Mikster4/thesis/Code/data/combined_rotation.png

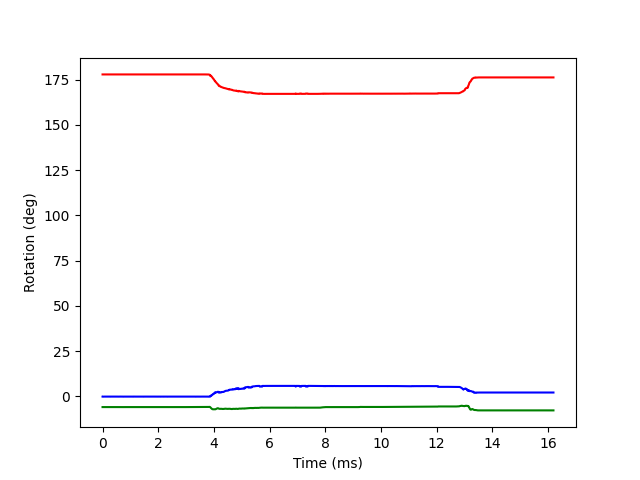
Code/data/combined_rotation.png
