Mikster4/thesis/Code/data/combined_rotation_relative.png

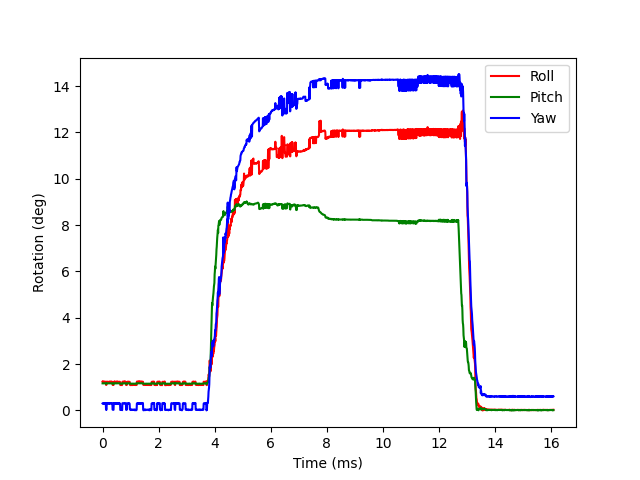
Code/data/combined_rotation_relative.png
