Mikster4/thesis/Code/data/Location_0_XY.PNG

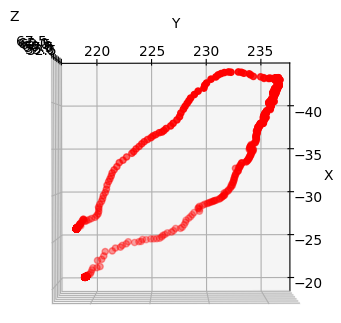
Code/data/Location_0_XY.PNG
