Mikster4/thesis/Code/data/Location_0_XZ.PNG

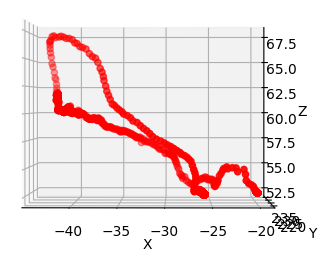
Code/data/Location_0_XZ.PNG
