Mikster4/thesis/Code/data/Location_0_YZ.PNG

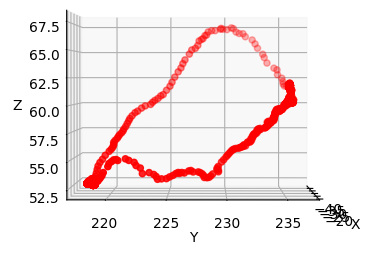
Code/data/Location_0_YZ.PNG
