Mikster4/thesis/Code/data/Max_Roll_Rotation_Norm.png

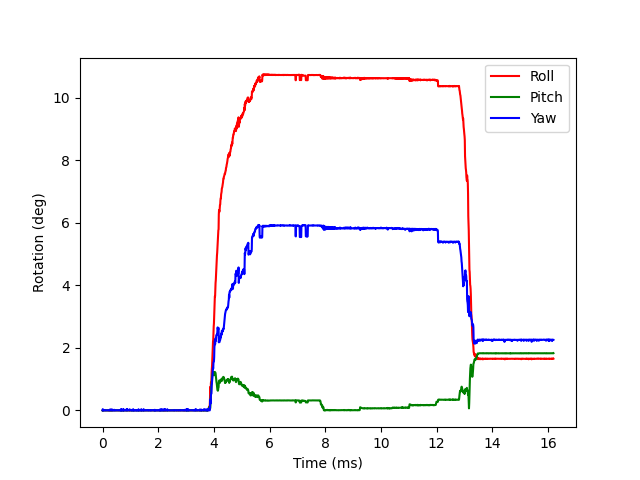
Code/data/Max_Roll_Rotation_Norm.png
