Mikster4/thesis/Code/data/Max_Yaw_Rotation_Raw.png

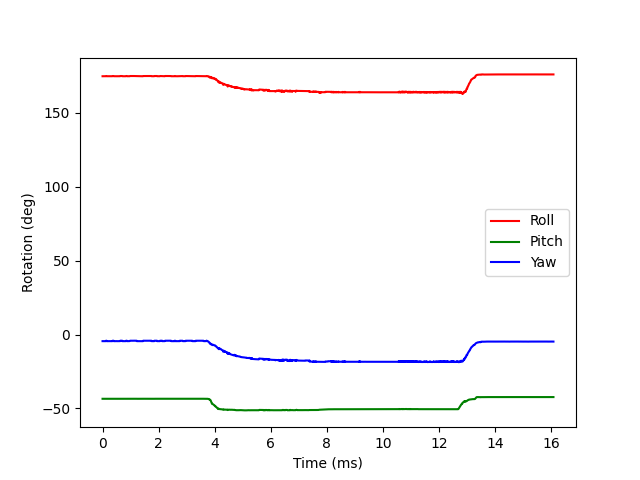
Code/data/Max_Yaw_Rotation_Raw.png
