Mikster4/thesis/CODE/data/pitch.png

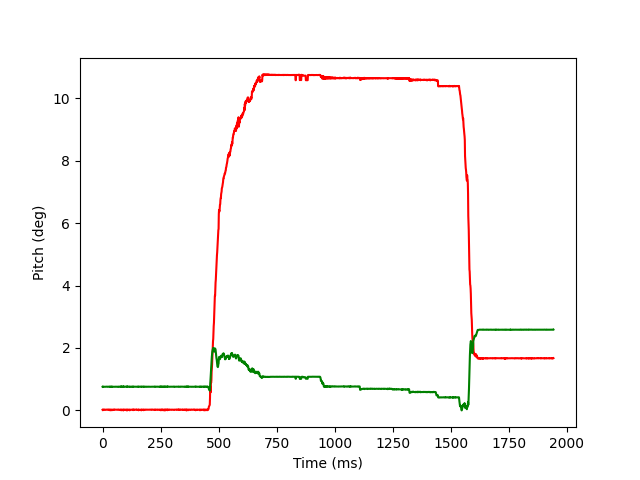
CODE/data/pitch.png
