Mikster4/thesis/Code/data/Platform_Linear.png

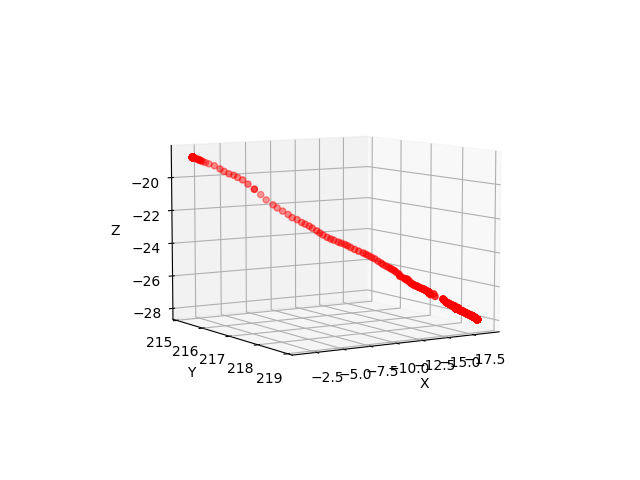
Code/data/Platform_Linear.png
