Mikster4/thesis/Code/data/platform_shape.PNG

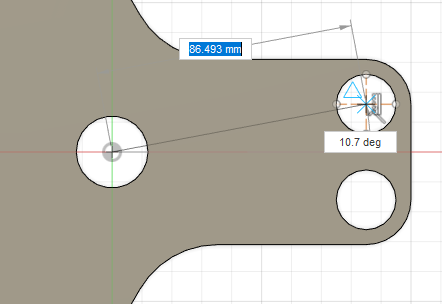
Code/data/platform_shape.PNG
