Mikster4/thesis/CODE/data/yaw.png

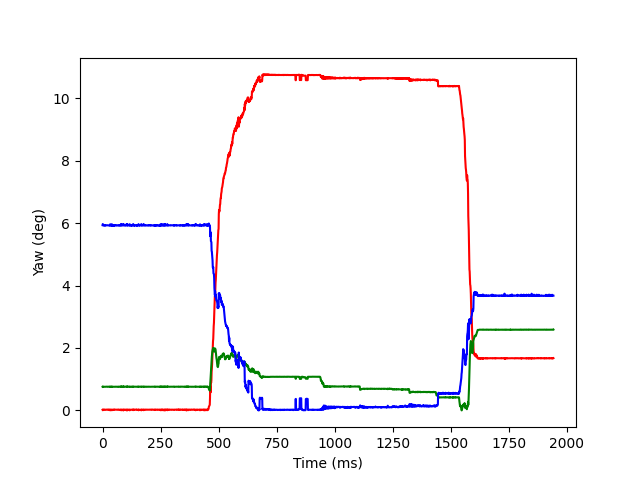
CODE/data/yaw.png
