Mikster4/thesis/IMG/coord.png

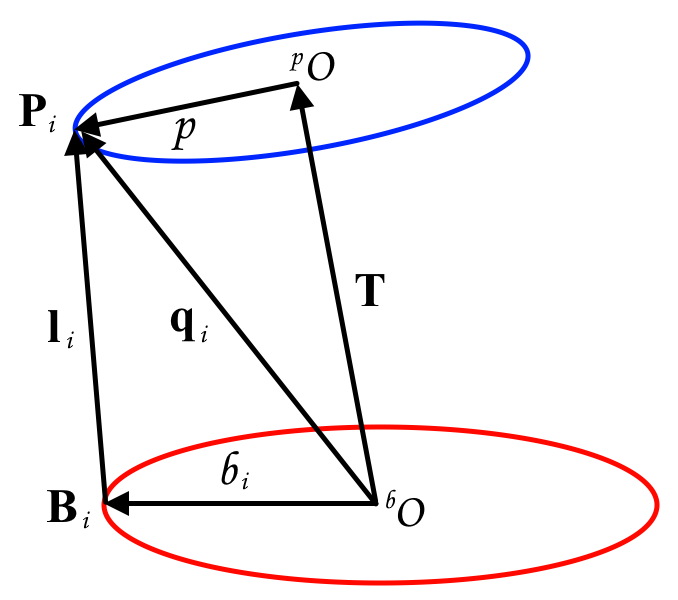
IMG/coord.png
