Mikster4/thesis/IMG/Photos/Cores/final_core_nozzle.jpg

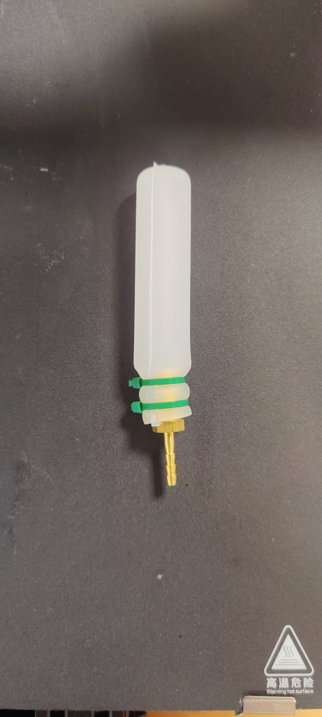
IMG/Photos/Cores/final_core_nozzle.jpg
