Mikster4/thesis/IMG/Photos/Cores/final_mold_cast.jpg

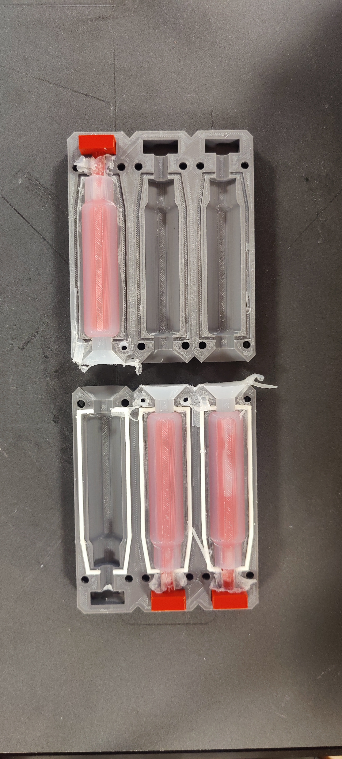
IMG/Photos/Cores/final_mold_cast.jpg
