Mikster4/thesis/IMG/Photos/Cores/IMG_20221129_133544.jpg

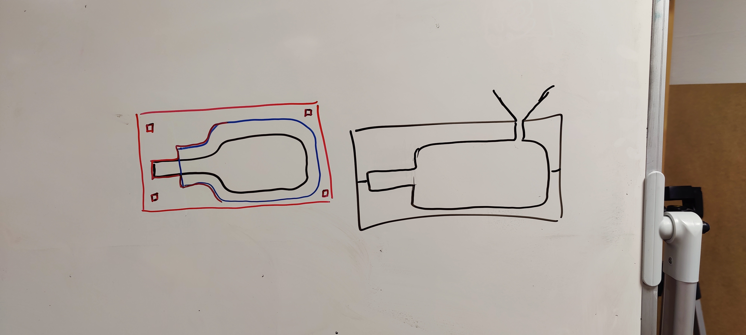
IMG/Photos/Cores/IMG_20221129_133544.jpg
