Mikster4/thesis/IMG/Photos/Cores/IMG_20221201_124950.jpg

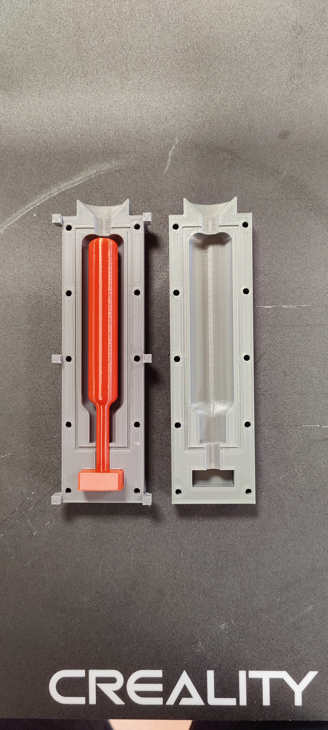
IMG/Photos/Cores/IMG_20221201_124950.jpg
