Mikster4/thesis/IMG/Photos/Cores/IMG_20221201_132122.jpg

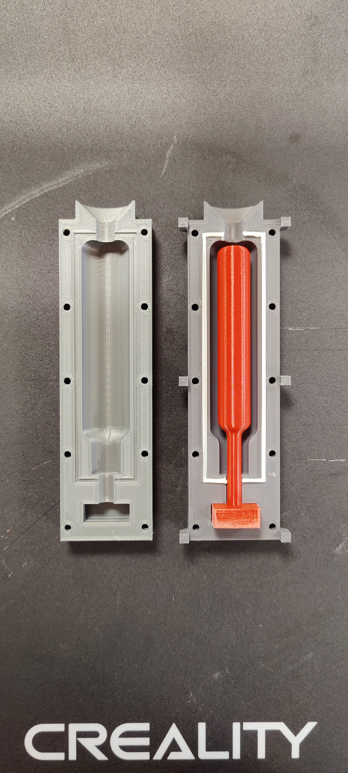
IMG/Photos/Cores/IMG_20221201_132122.jpg
