Mikster4/thesis/IMG/Photos/Cores/IMG_20221201_132601.jpg

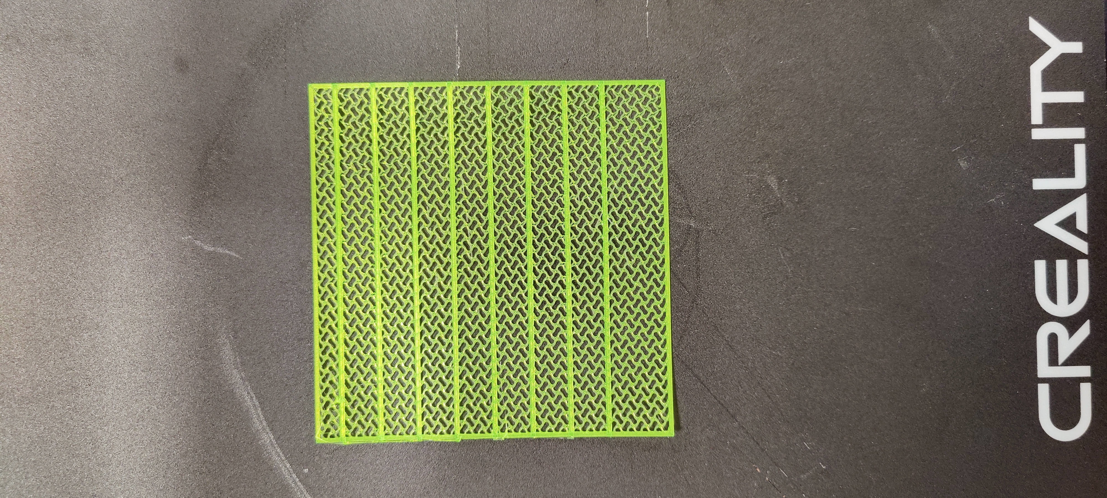
IMG/Photos/Cores/IMG_20221201_132601.jpg
