Mikster4/thesis/IMG/Photos/Cores/IMG_20221201_133057.jpg

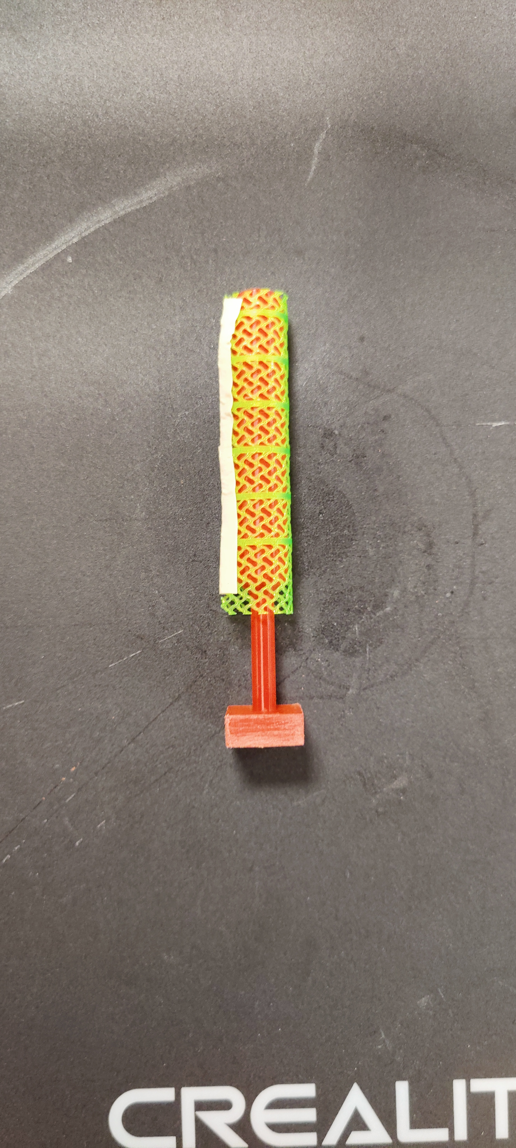
IMG/Photos/Cores/IMG_20221201_133057.jpg
