Mikster4/thesis/IMG/Photos/Cores/IMG_20221201_133152.jpg

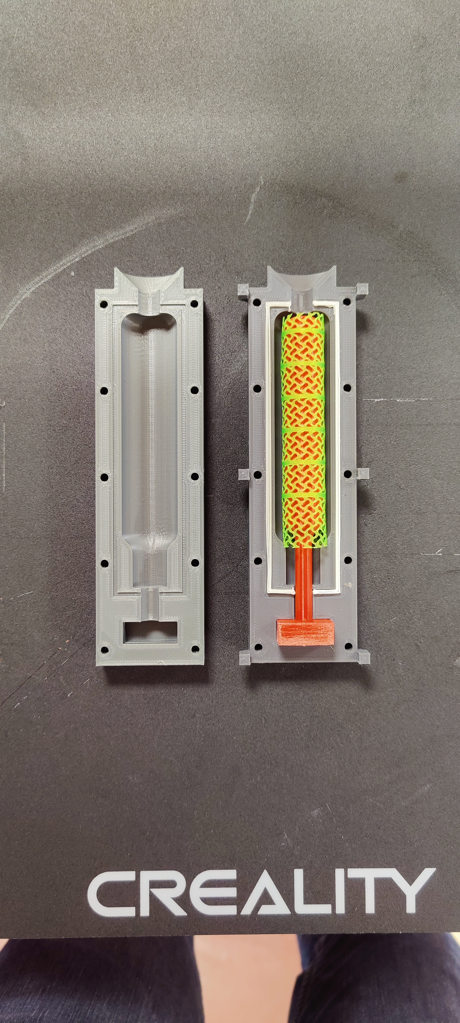
IMG/Photos/Cores/IMG_20221201_133152.jpg
