Mikster4/thesis/IMG/Photos/Cores/IMG_20230104_114442.jpg

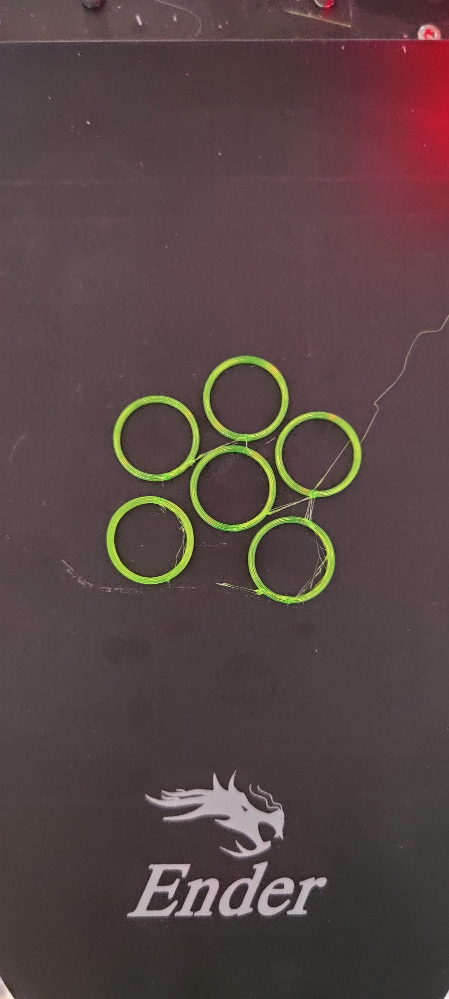
IMG/Photos/Cores/IMG_20230104_114442.jpg
