Mikster4/thesis/IMG/Photos/Cores/IMG_20230104_140045.jpg

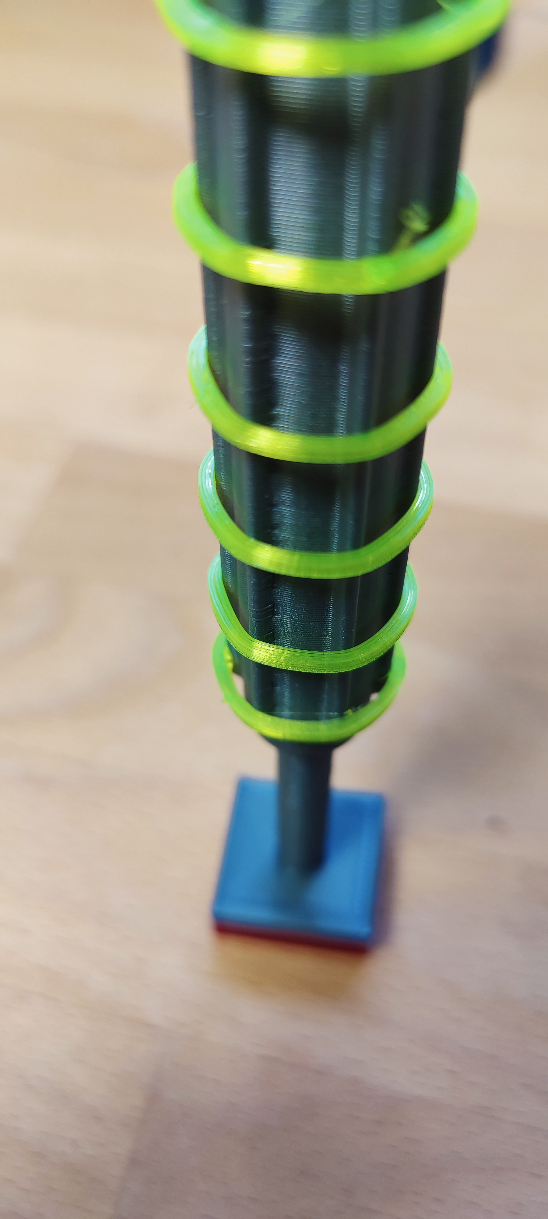
IMG/Photos/Cores/IMG_20230104_140045.jpg
