Mikster4/thesis/IMG/Photos/Cores/IMG_20230104_140136.jpg

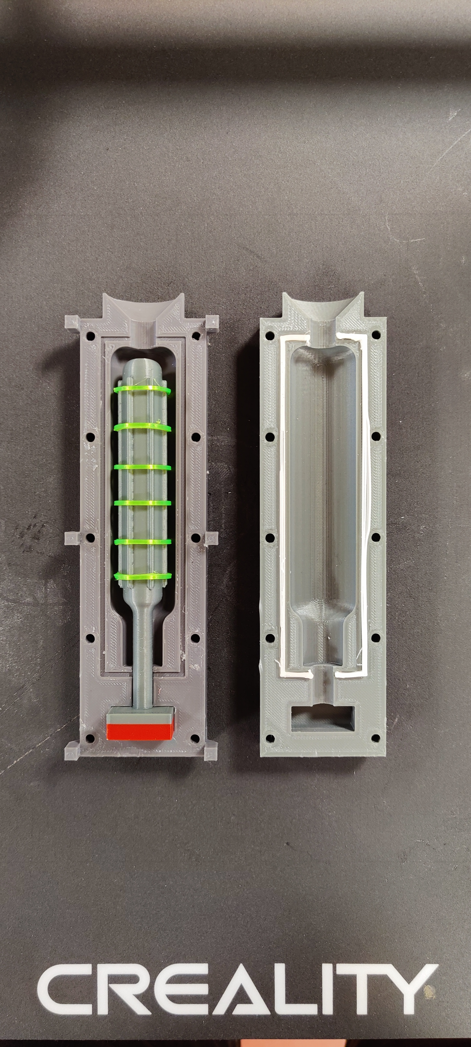
IMG/Photos/Cores/IMG_20230104_140136.jpg
