Mikster4/thesis/IMG/Photos/Cores/IMG_20230105_142405.jpg

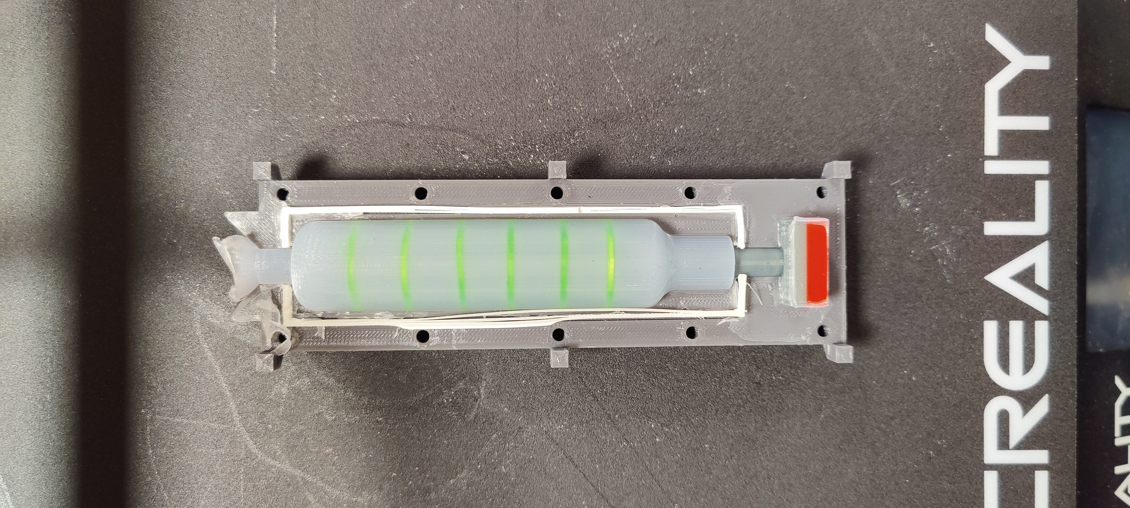
IMG/Photos/Cores/IMG_20230105_142405.jpg
