Mikster4/thesis/IMG/Photos/Cores/IMG_20230105_143052.jpg

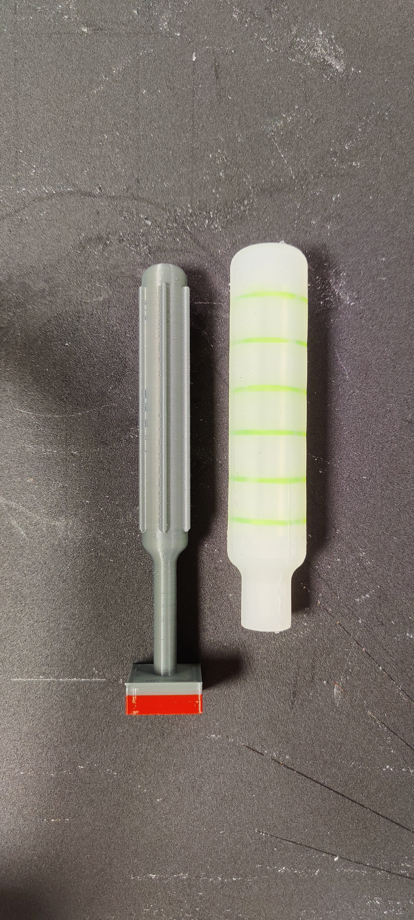
IMG/Photos/Cores/IMG_20230105_143052.jpg
