Mikster4/thesis/IMG/Photos/Cores/IMG_20230105_143107.jpg

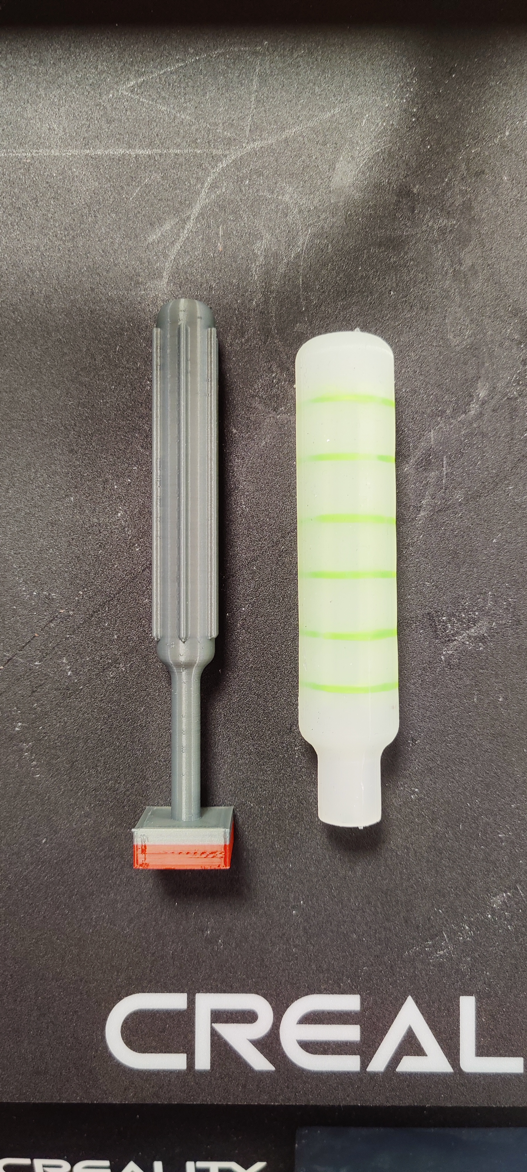
IMG/Photos/Cores/IMG_20230105_143107.jpg
