Mikster4/thesis/IMG/Photos/Cores/IMG_20230112_104922.jpg

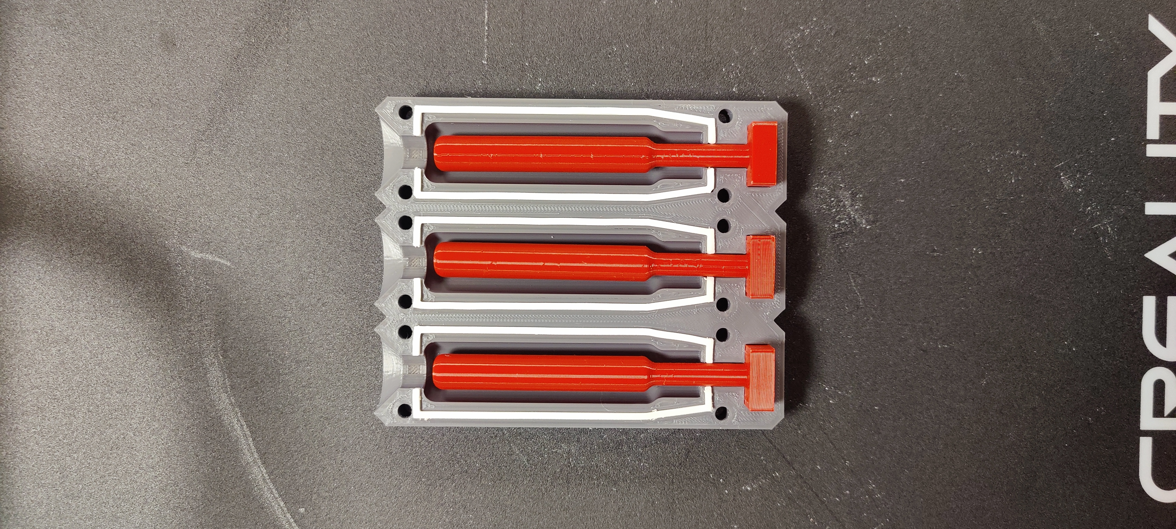
IMG/Photos/Cores/IMG_20230112_104922.jpg
