Mikster4/thesis/IMG/Photos/Cores/IMG_20230112_104932.jpg

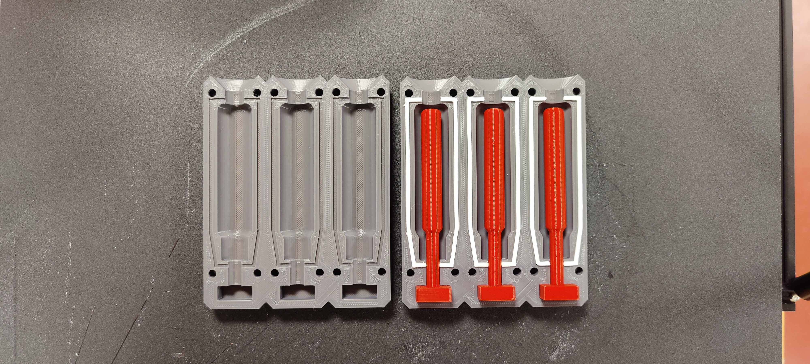
IMG/Photos/Cores/IMG_20230112_104932.jpg
