Mikster4/thesis/IMG/Photos/Cores/IMG_20230119_000719.jpg

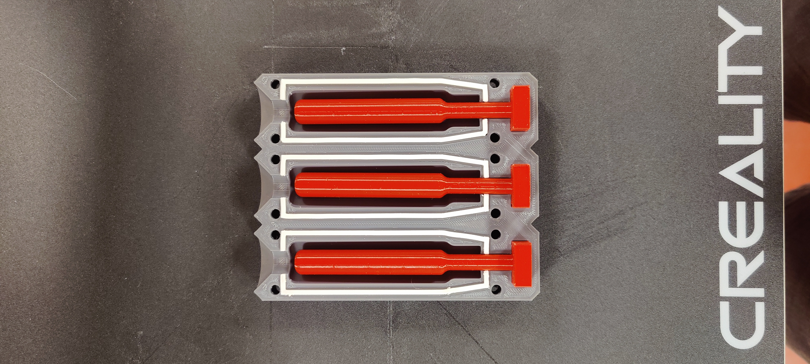
IMG/Photos/Cores/IMG_20230119_000719.jpg
