Mikster4/thesis/IMG/Photos/Cores/IMG_20230119_070848.jpg

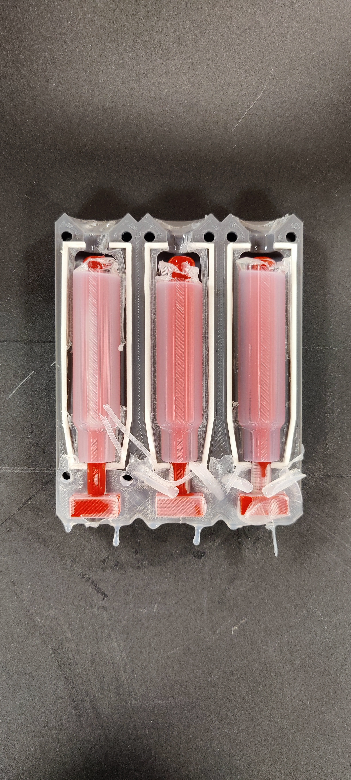
IMG/Photos/Cores/IMG_20230119_070848.jpg
