Mikster4/thesis/IMG/Photos/Cores/IMG_20230119_092744.jpg

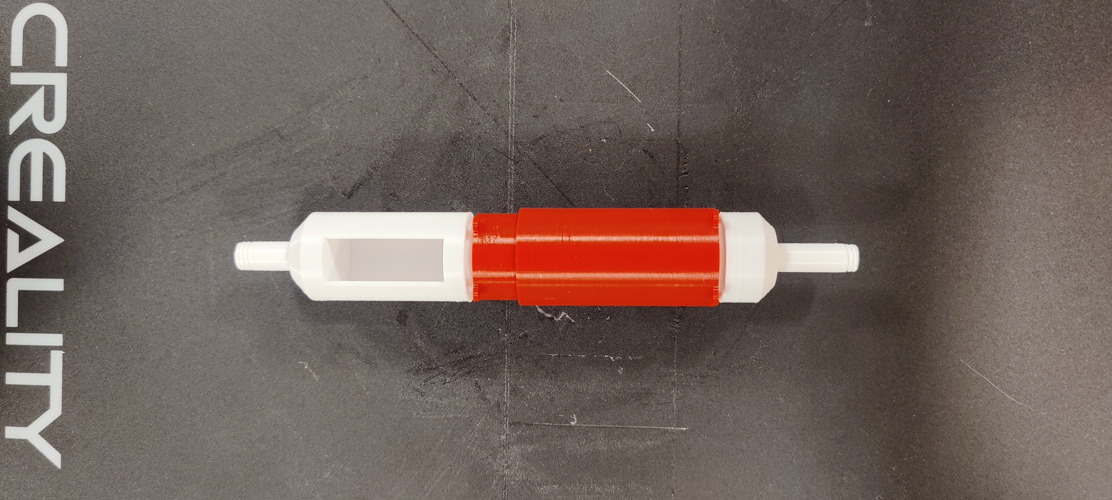
IMG/Photos/Cores/IMG_20230119_092744.jpg
