Mikster4/thesis/IMG/Photos/Cores/IMG_20230119_103604.jpg

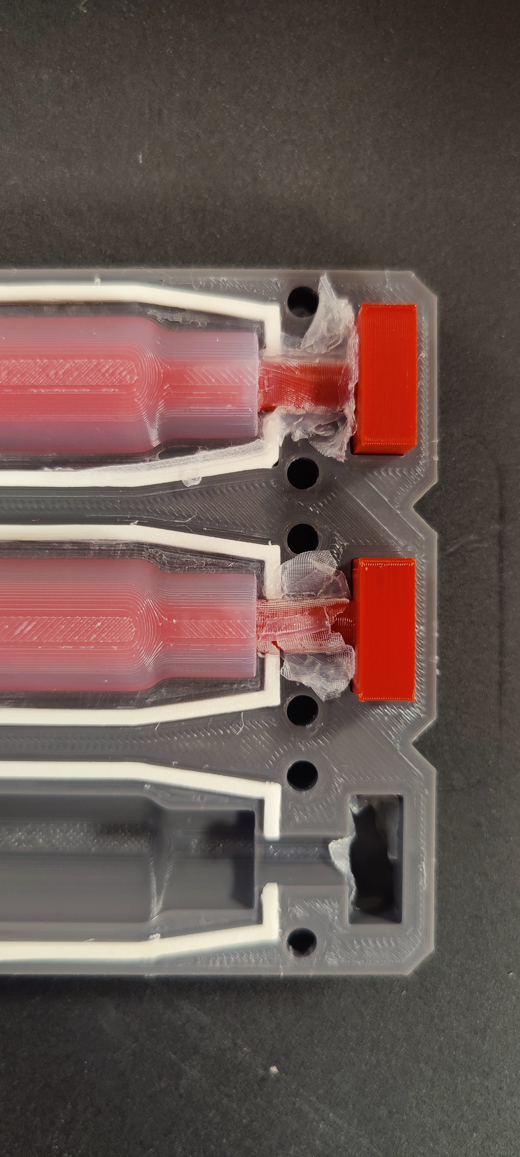
IMG/Photos/Cores/IMG_20230119_103604.jpg
