Mikster4/thesis/IMG/Photos/Cores/IMG_20230119_103908.jpg

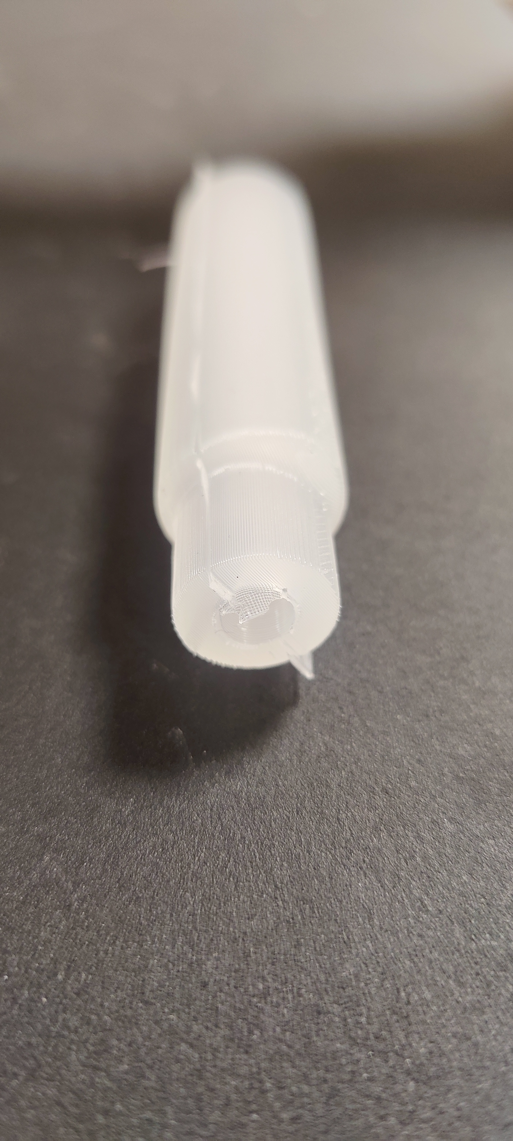
IMG/Photos/Cores/IMG_20230119_103908.jpg
