Mikster4/thesis/IMG/Photos/Cores/IMG_20230221_175424.jpg

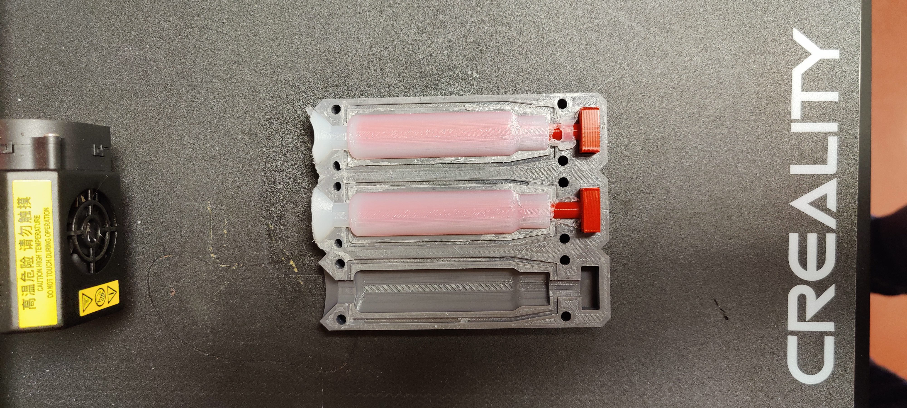
IMG/Photos/Cores/IMG_20230221_175424.jpg
