Mikster4/thesis/IMG/Photos/Cores/IMG_20230221_175434.jpg

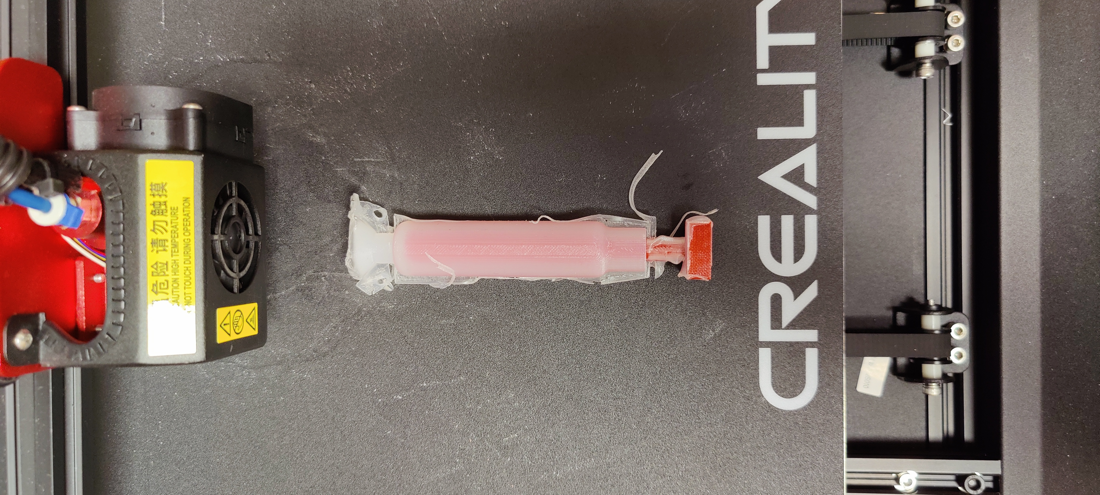
IMG/Photos/Cores/IMG_20230221_175434.jpg
