Mikster4/thesis/IMG/Photos/Cores/mesh_airtight.jpg

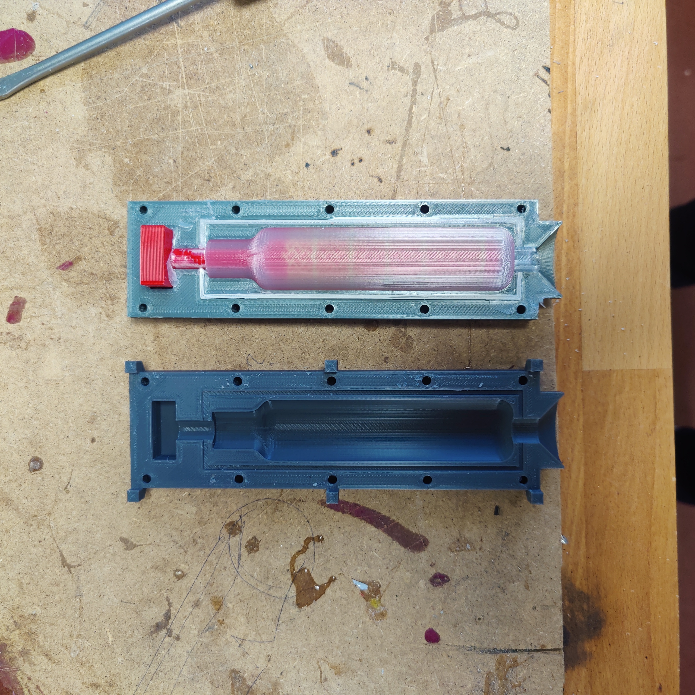
IMG/Photos/Cores/mesh_airtight.jpg
