Mikster4/thesis/IMG/Photos/Cores/mesh_fail_1.jpg

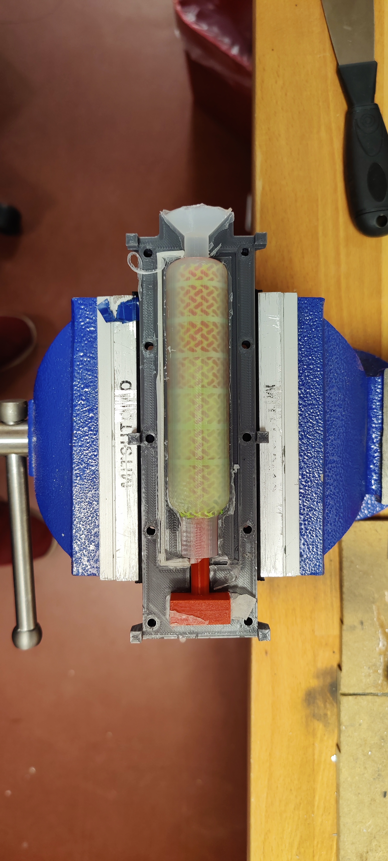
IMG/Photos/Cores/mesh_fail_1.jpg
