Mikster4/thesis/IMG/Photos/Cores/tpu_rings_fail.jpg

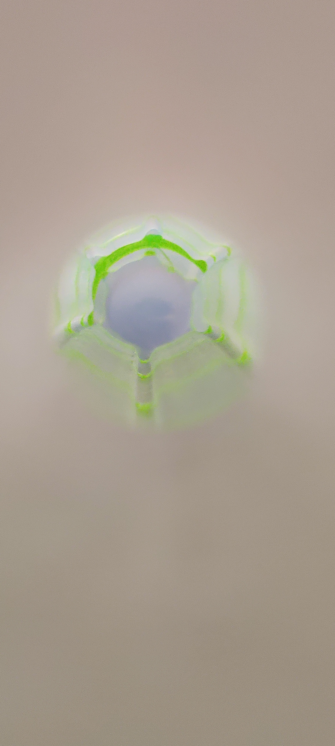
IMG/Photos/Cores/tpu_rings_fail.jpg
