Mikster4/thesis/IMG/Photos/Cores/tpu_rings_finish.jpg

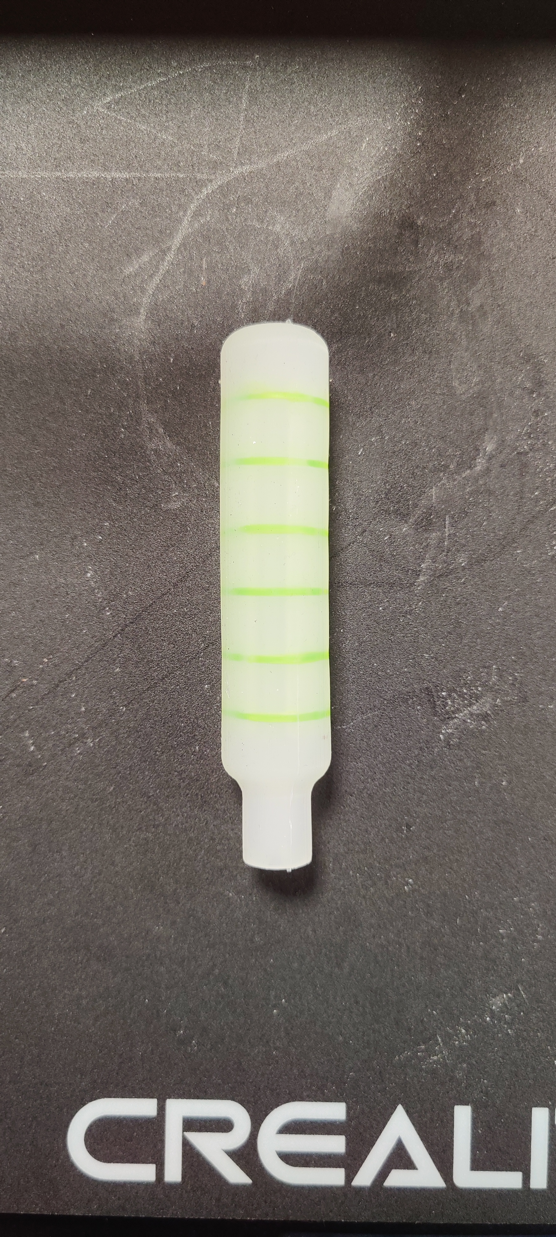
IMG/Photos/Cores/tpu_rings_finish.jpg
