Mikster4/thesis/IMG/Photos/Cores/tpu_rings_insert.jpg

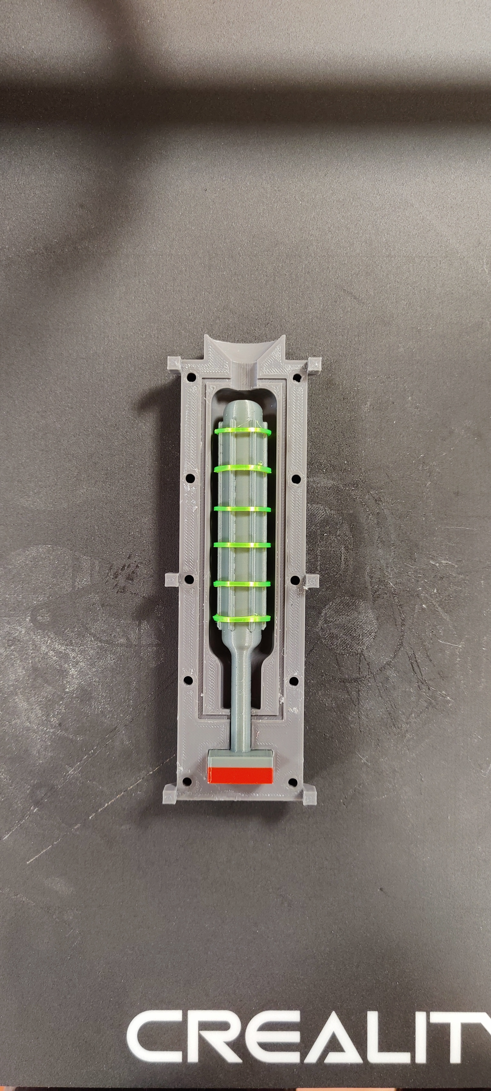
IMG/Photos/Cores/tpu_rings_insert.jpg
