Mikster4/thesis/IMG/Photos/Electrical/IMG_20230119_111654.jpg

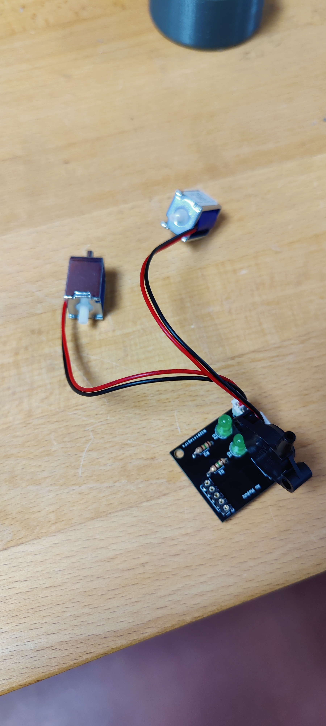
IMG/Photos/Electrical/IMG_20230119_111654.jpg
