Mikster4/thesis/IMG/Photos/Electrical/IMG_20230119_111658.jpg

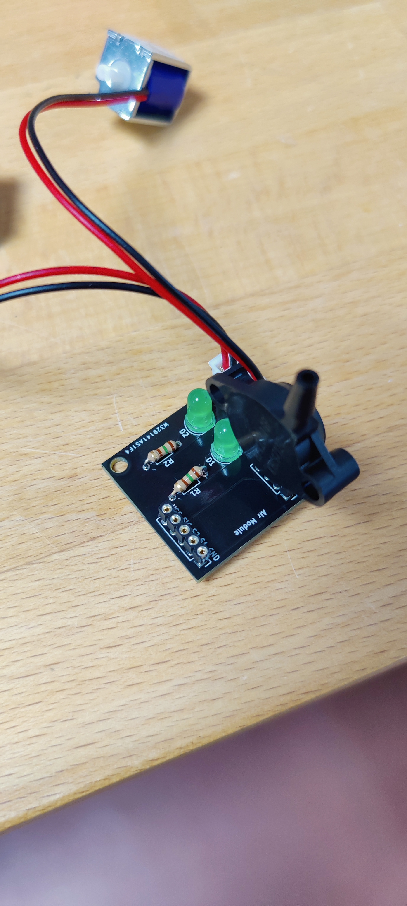
IMG/Photos/Electrical/IMG_20230119_111658.jpg
