Mikster4/thesis/IMG/Photos/Electrical/IMG_20230218_131912.jpg

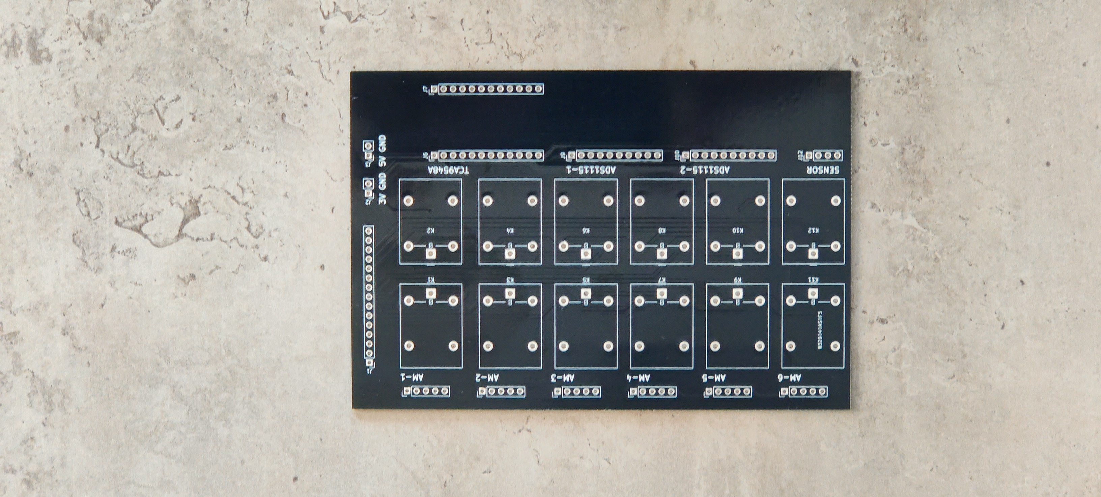
IMG/Photos/Electrical/IMG_20230218_131912.jpg
