Mikster4/thesis/IMG/Photos/Electrical/IMG_20230222_151632.jpg

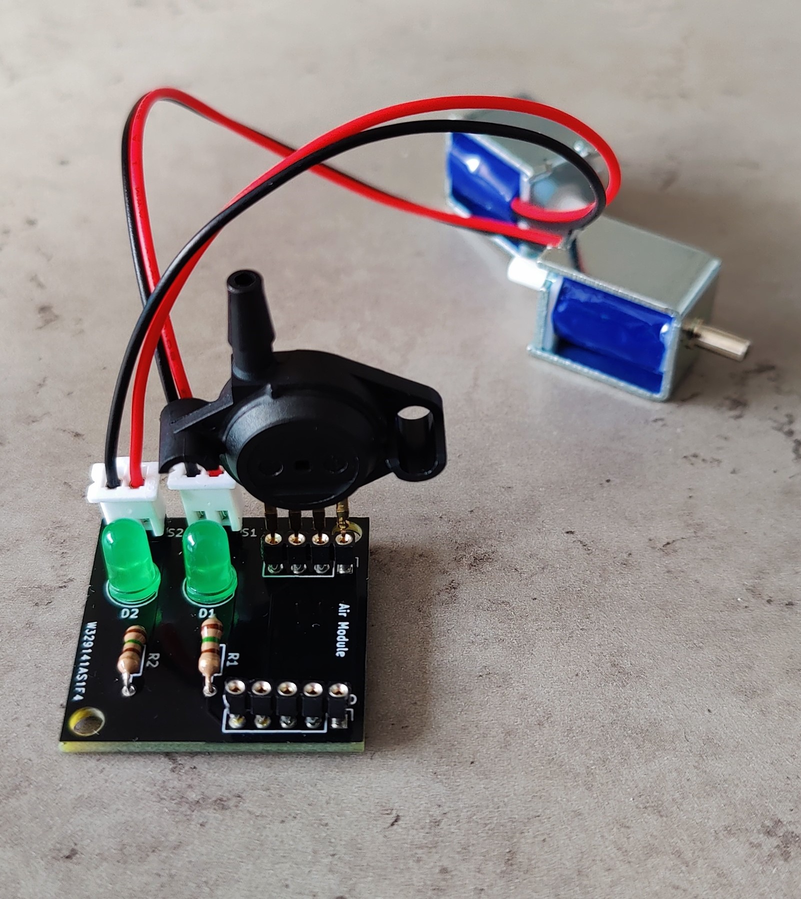
IMG/Photos/Electrical/IMG_20230222_151632.jpg
