Mikster4/thesis/IMG/Photos/Electrical/IMG_20230222_151733.jpg

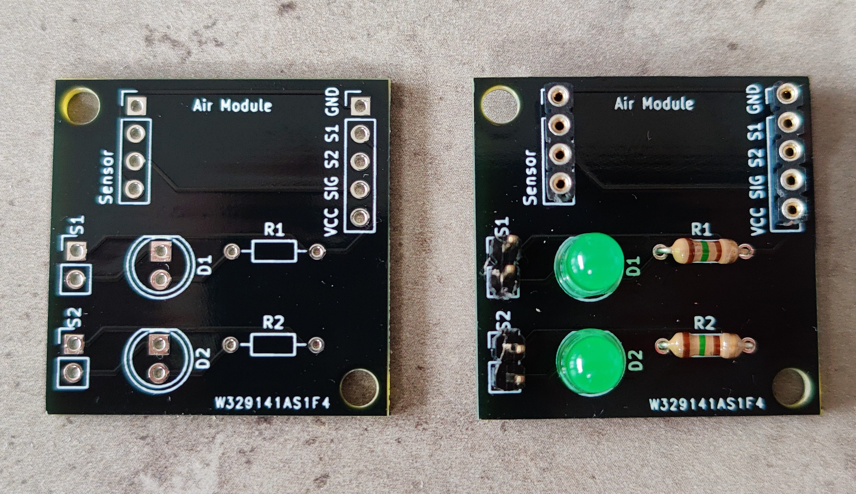
IMG/Photos/Electrical/IMG_20230222_151733.jpg
