Mikster4/thesis/IMG/Photos/OptiTrack/roll_max.png

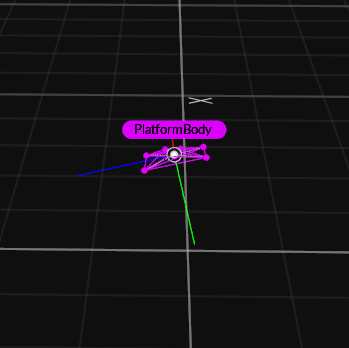
IMG/Photos/OptiTrack/roll_max.png
