Mikster4/thesis/IMG/Photos/OptiTrack/roll_min.png

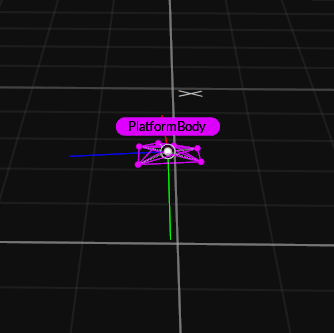
IMG/Photos/OptiTrack/roll_min.png
