Mikster4/thesis/IMG/Photos/OptiTrack/Screenshot 2023-03-09 115746.png

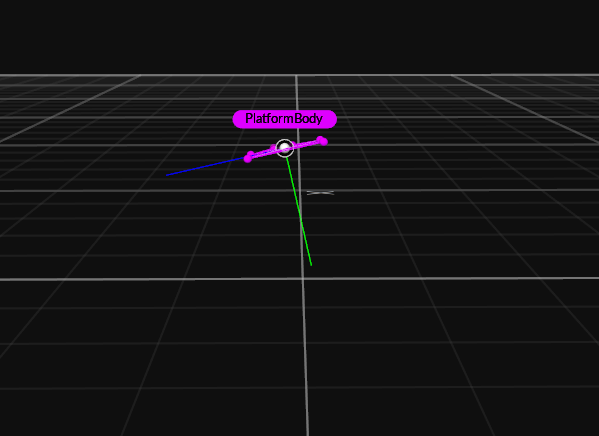
IMG/Photos/OptiTrack/Screenshot 2023-03-09 115746.png
