Mikster4/thesis/IMG/Photos/OptiTrack/yaw_max.png

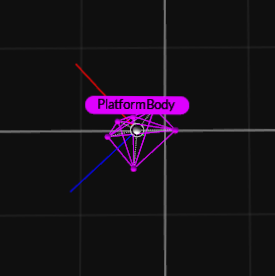
IMG/Photos/OptiTrack/yaw_max.png
