Mikster4/thesis/IMG/Photos/Platform/IMG_20230112_014713.jpg

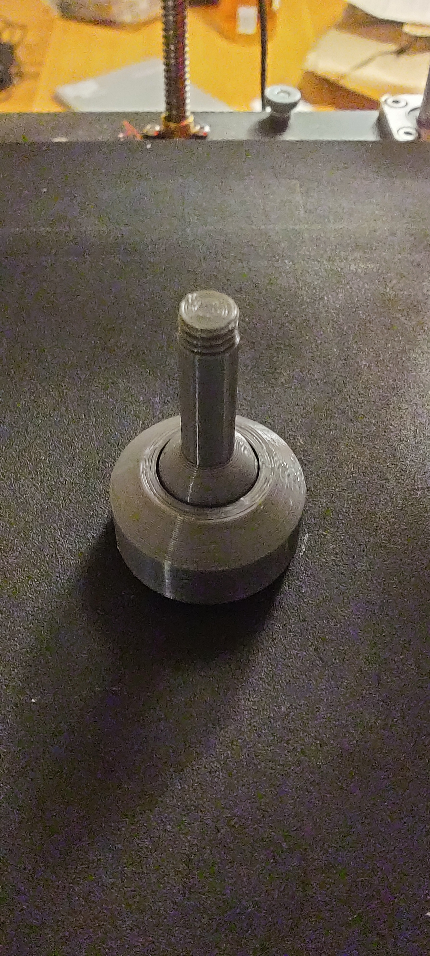
IMG/Photos/Platform/IMG_20230112_014713.jpg
