Mikster4/thesis/IMG/Photos/Platform/IMG_20230112_025201.jpg

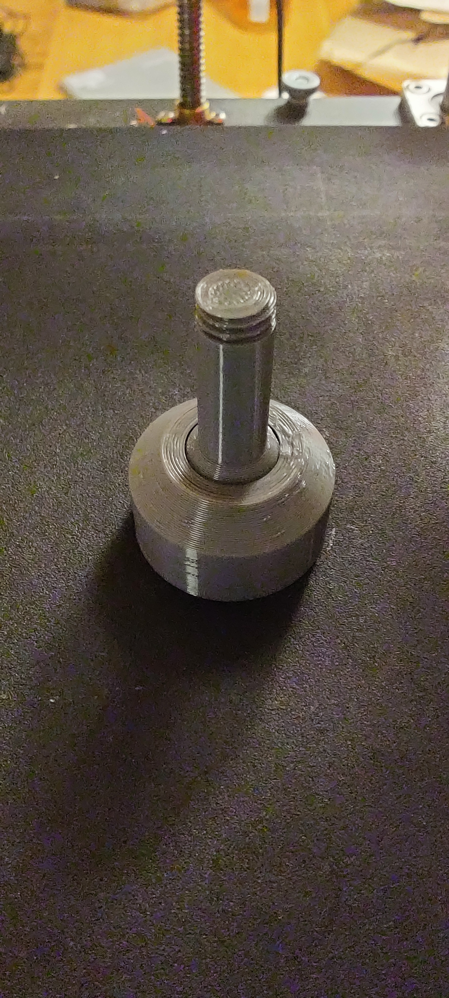
IMG/Photos/Platform/IMG_20230112_025201.jpg
