Mikster4/thesis/IMG/Photos/Platform/IMG_20230119_092630.jpg

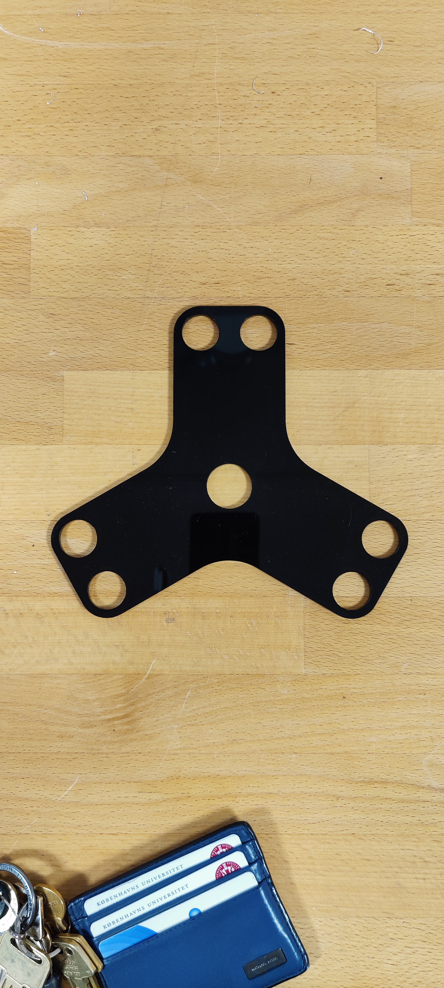
IMG/Photos/Platform/IMG_20230119_092630.jpg
