Mikster4/thesis/IMG/Photos/Platform/IMG_20230119_111612.jpg

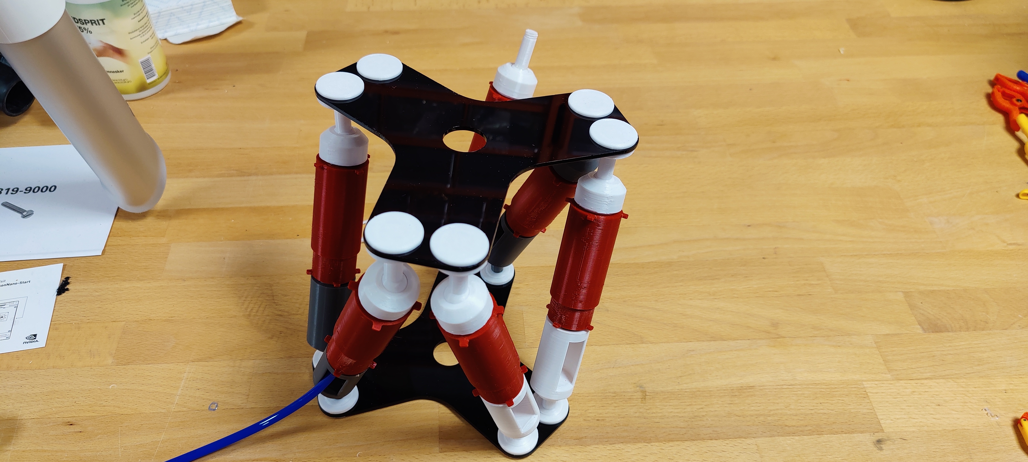
IMG/Photos/Platform/IMG_20230119_111612.jpg
