Mikster4/thesis/IMG/Photos/Platform/IMG_20230119_111621.jpg

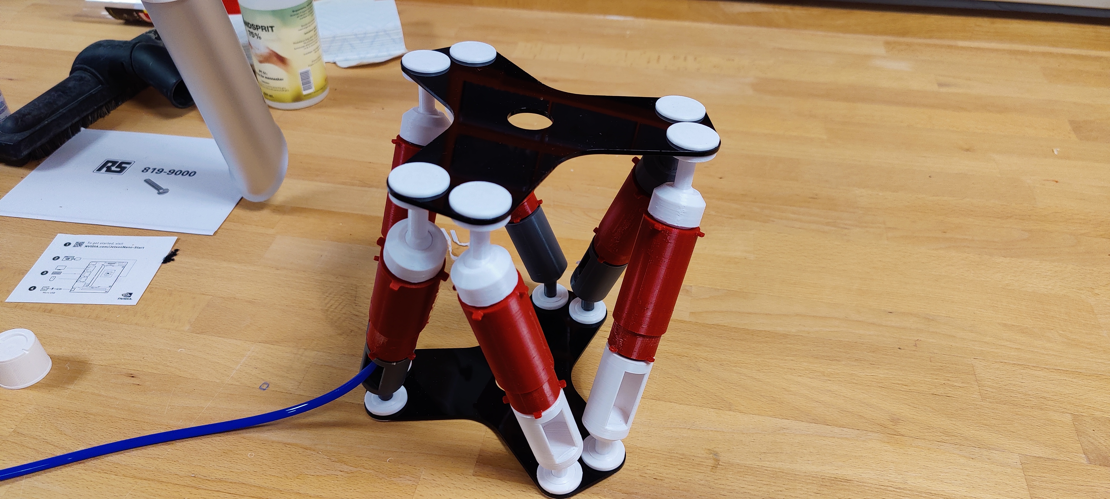
IMG/Photos/Platform/IMG_20230119_111621.jpg
