Mikster4/thesis/IMG/Photos/Platform/IMG_20230222_152040.jpg

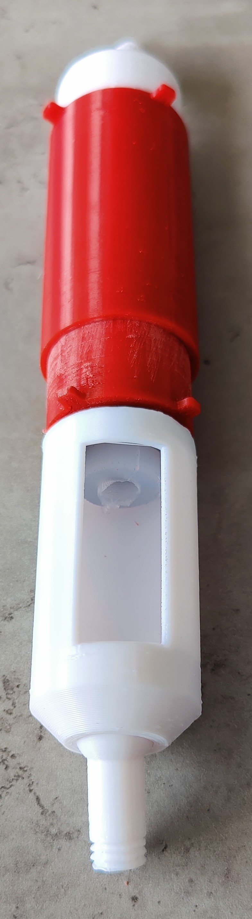
IMG/Photos/Platform/IMG_20230222_152040.jpg
