Mikster4/thesis/IMG/Photos/Platform/IMG_20230222_152114.jpg

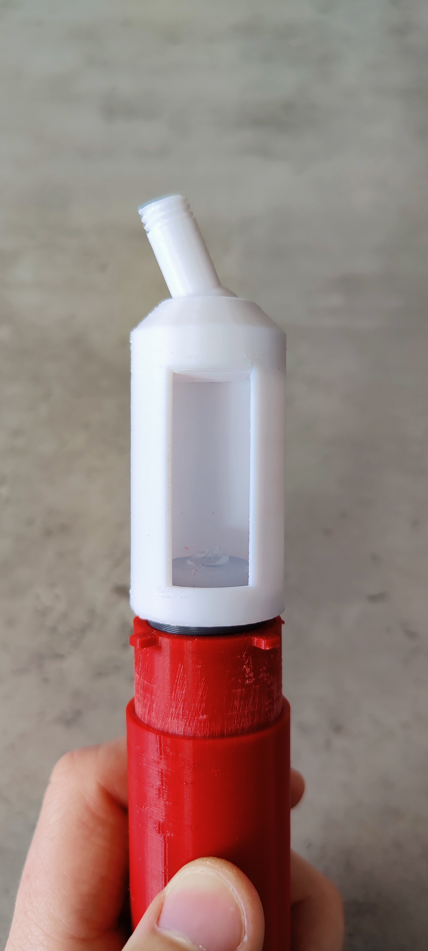
IMG/Photos/Platform/IMG_20230222_152114.jpg
