Mikster4/thesis/IMG/Photos/Platform/IMG_20230222_152124.jpg

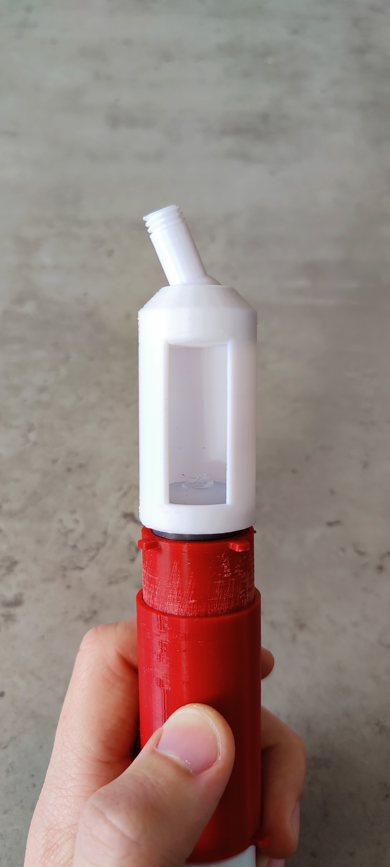
IMG/Photos/Platform/IMG_20230222_152124.jpg
