Mikster4/thesis/IMG/Photos/Platform/IMG_20230222_152329.jpg

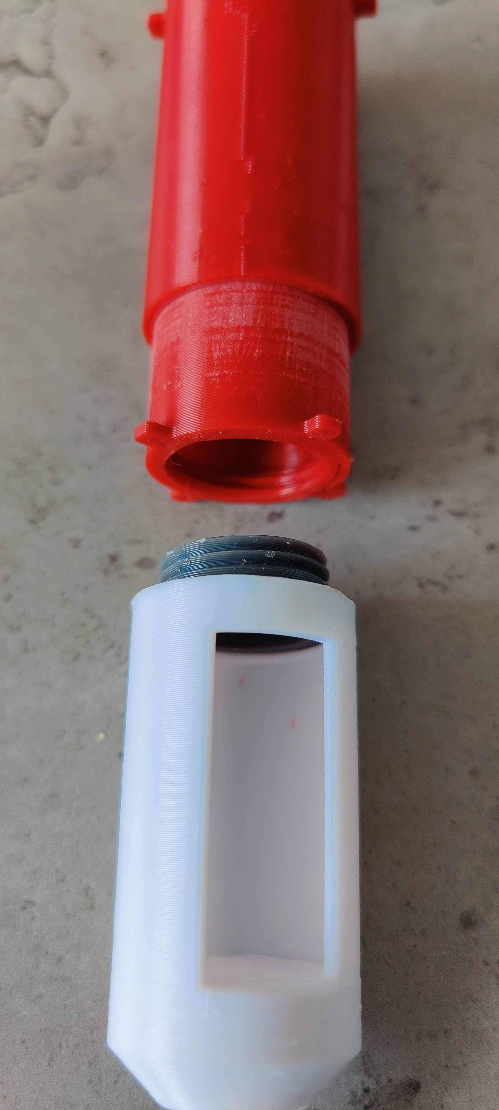
IMG/Photos/Platform/IMG_20230222_152329.jpg
