Mikster4/thesis/IMG/Renders/poc_0.png

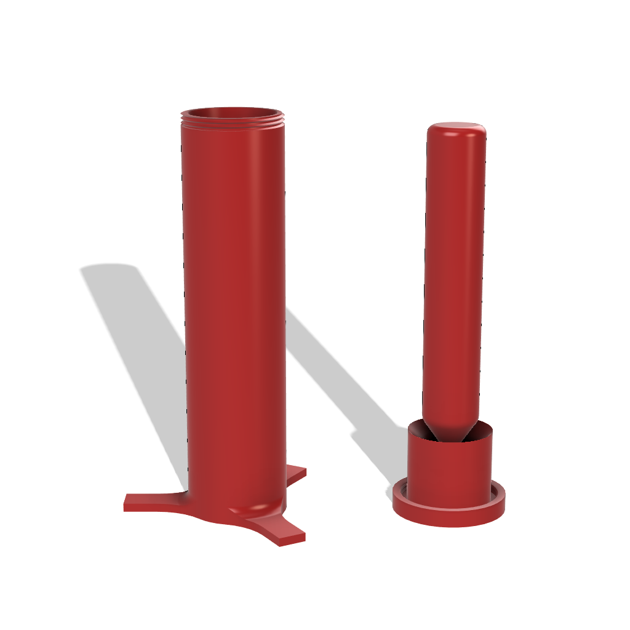
IMG/Renders/poc_0.png
