Mikster4/thesis/IMG/Renders/POC_0_insert.PNG

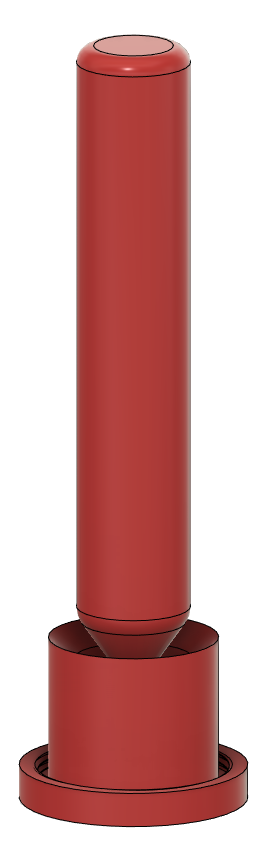
IMG/Renders/POC_0_insert.PNG
