Mikster4/thesis/IMG/Renders/POC_0_insert_cut.PNG

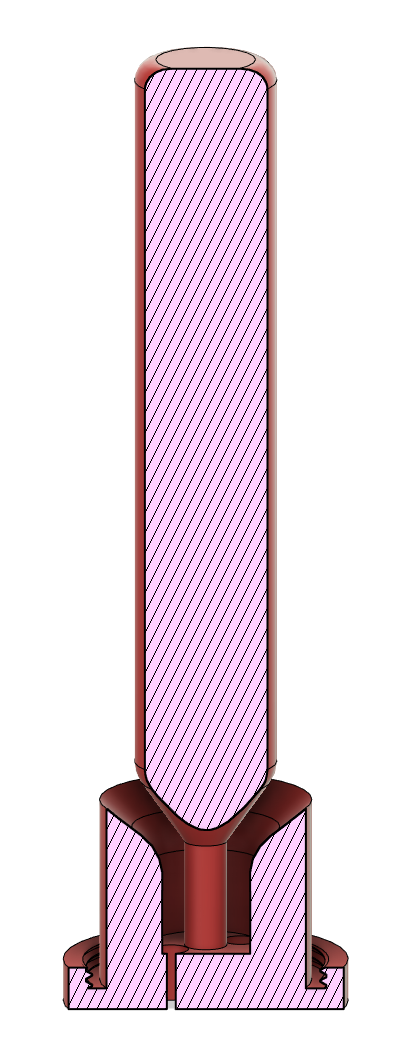
IMG/Renders/POC_0_insert_cut.PNG
