Mikster4/thesis/IMG/Renders/POC_0_shell.PNG

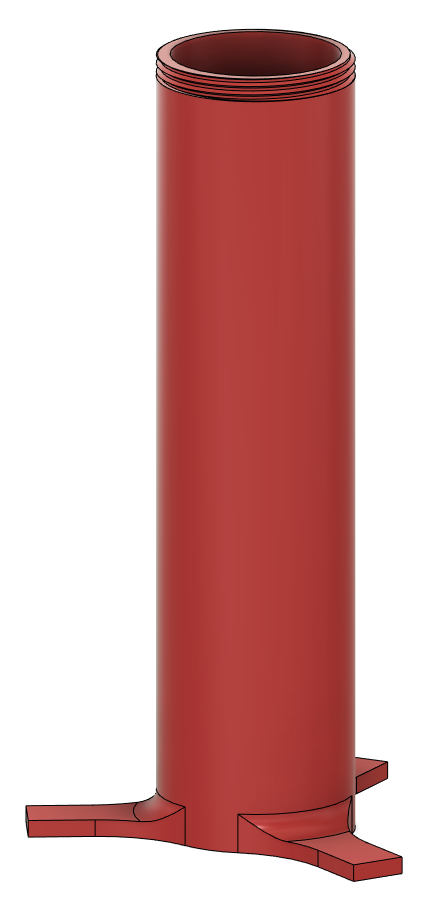
IMG/Renders/POC_0_shell.PNG
