Mikster4/thesis/IMG/Renders/POC_0_shell_cut.PNG

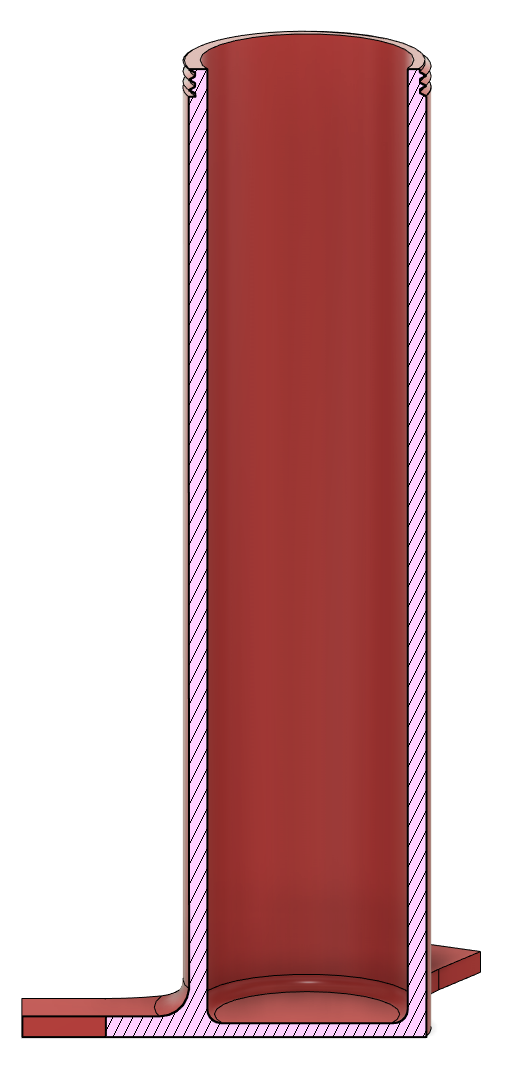
IMG/Renders/POC_0_shell_cut.PNG
