Mikster4/thesis/IMG/Renders/POC_1_Base.PNG

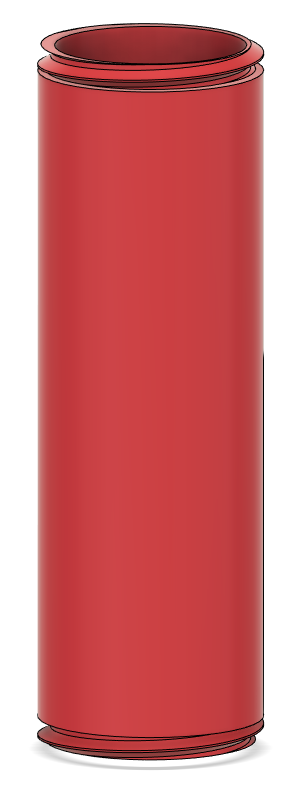
IMG/Renders/POC_1_Base.PNG
