Mikster4/thesis/IMG/Renders/POC_1_Cap.PNG

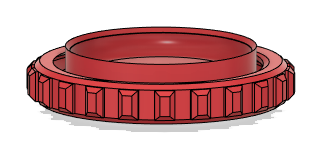
IMG/Renders/POC_1_Cap.PNG
