Mikster4/thesis/IMG/Renders/POC_1_Insert.PNG

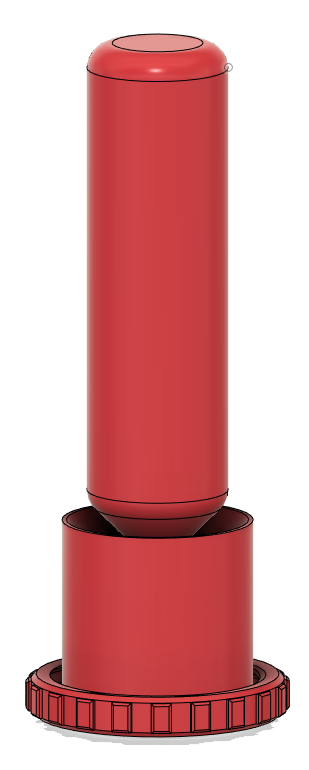
IMG/Renders/POC_1_Insert.PNG
