Mikster4/thesis/IMG/Renders/POC_1_open_top.PNG

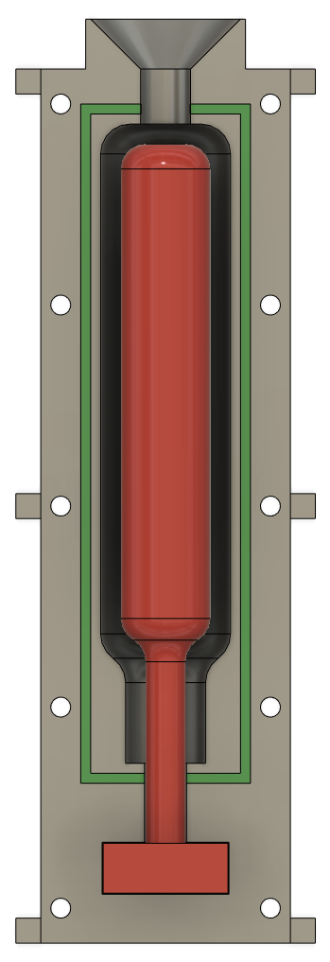
IMG/Renders/POC_1_open_top.PNG
