Mikster4/thesis/IMG/Renders/POC_2_Closed.PNG

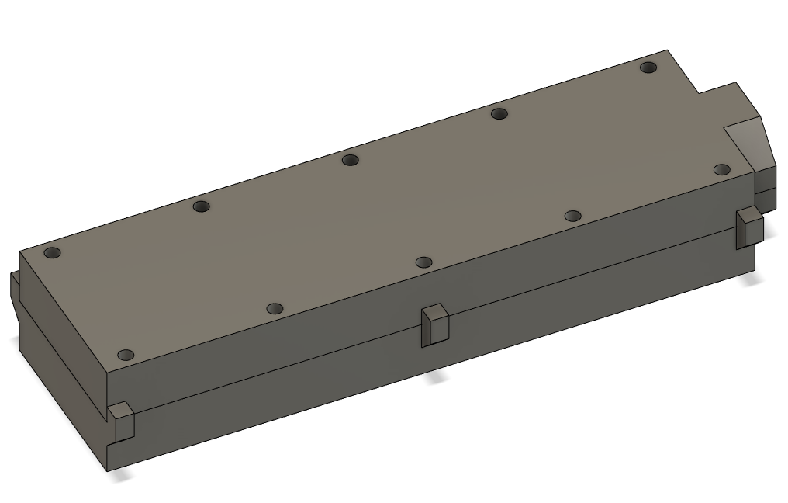
IMG/Renders/POC_2_Closed.PNG
