Mikster4/thesis/IMG/Renders/POC_2_Exploded.PNG

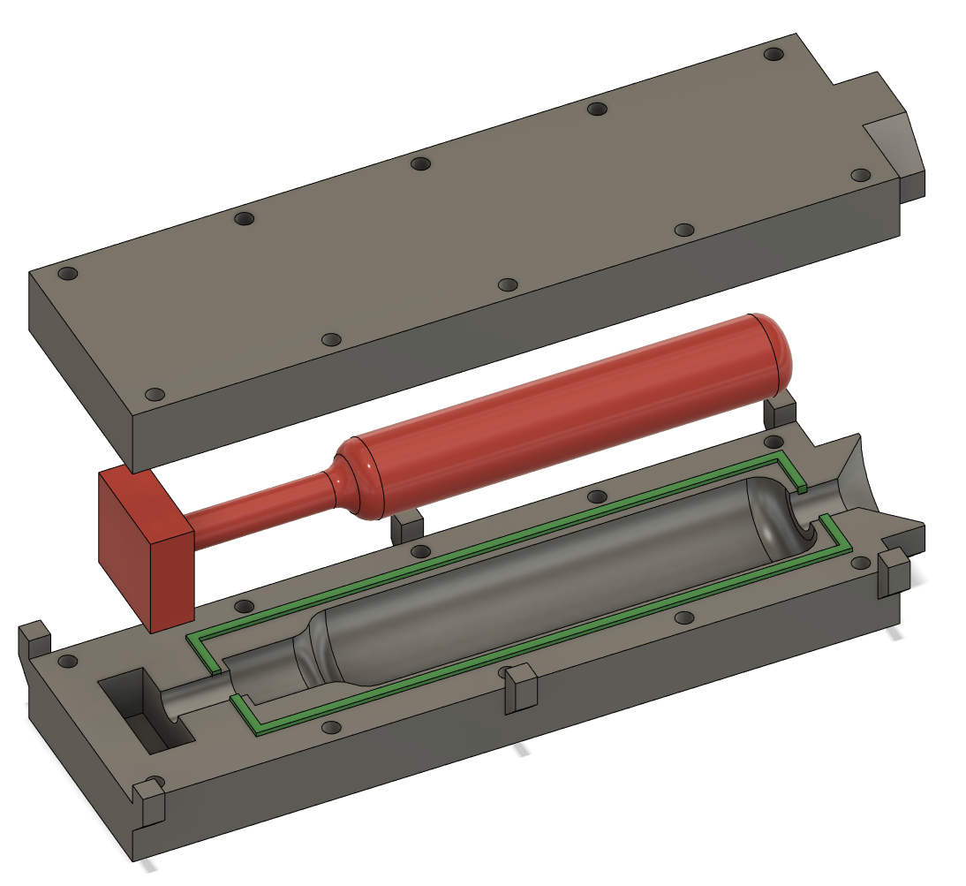
IMG/Renders/POC_2_Exploded.PNG
