Mikster4/thesis/IMG/Renders/POC_2_open_top.PNG

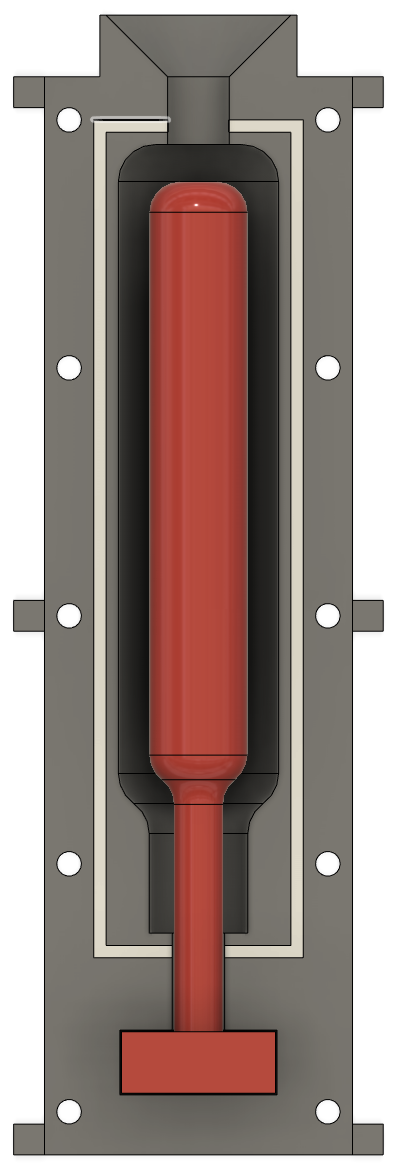
IMG/Renders/POC_2_open_top.PNG
