Mikster4/thesis/IMG/Renders/POC_3_Ring_Side.PNG

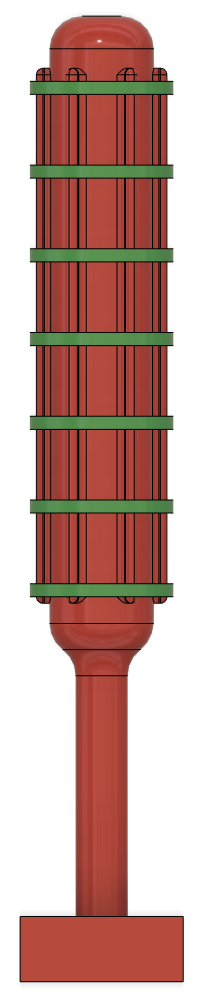
IMG/Renders/POC_3_Ring_Side.PNG
