Mikster4/thesis/IMG/Renders/POC_3_Ring_Top.PNG

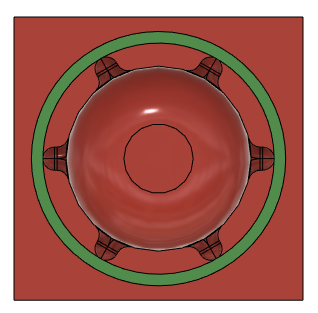
IMG/Renders/POC_3_Ring_Top.PNG
