Mikster4/thesis/IMG/Renders/POC_4_Piston.PNG

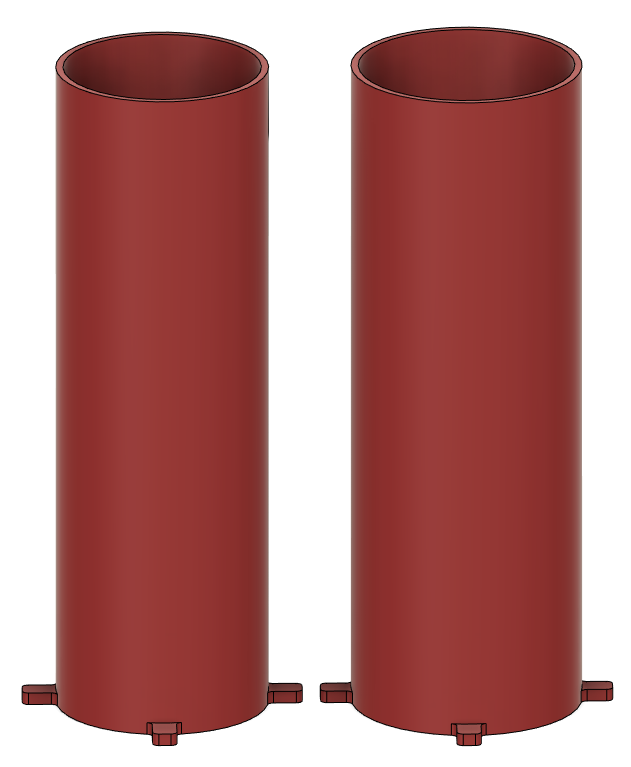
IMG/Renders/POC_4_Piston.PNG
