Mikster4/thesis/IMG/Renders/POC_5_Connector.PNG

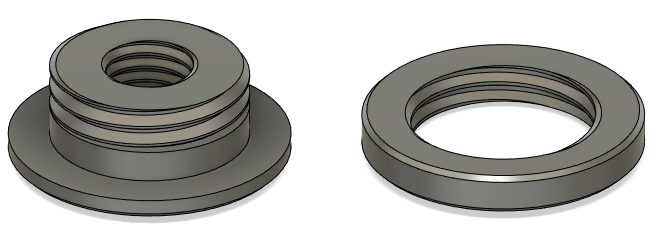
IMG/Renders/POC_5_Connector.PNG
