Mikster4/thesis/IMG/Renders/POC_5_Flexer.PNG

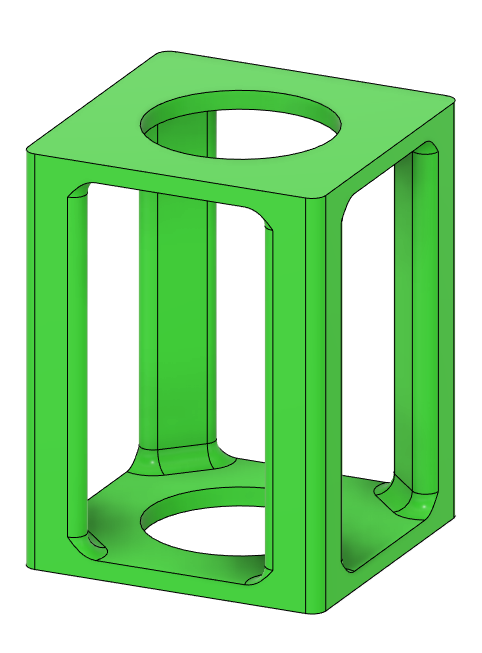
IMG/Renders/POC_5_Flexer.PNG
