Mikster4/thesis/IMG/Renders/POC_5_Joint_base.PNG

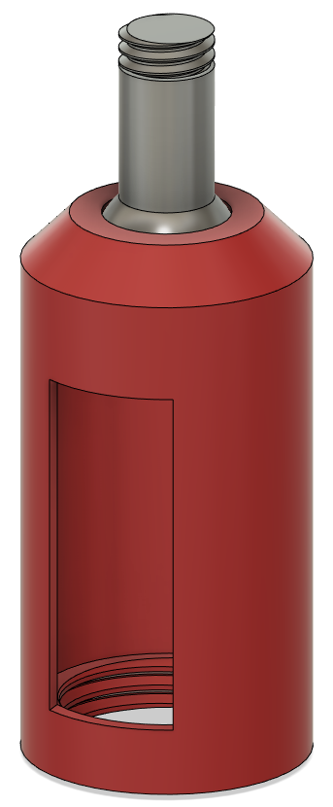
IMG/Renders/POC_5_Joint_base.PNG
