Mikster4/thesis/IMG/Renders/POC_5_Joint_Platform.PNG

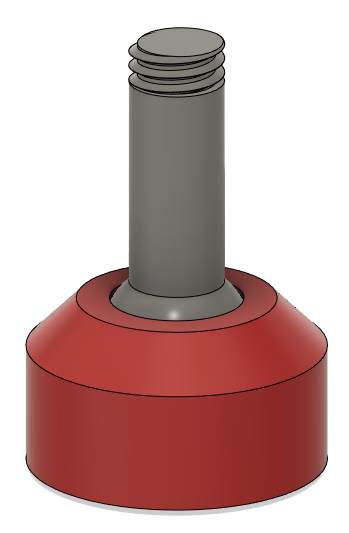
IMG/Renders/POC_5_Joint_Platform.PNG
