Mikster4/thesis/IMG/Renders/POC_5_Mold_Insert.PNG

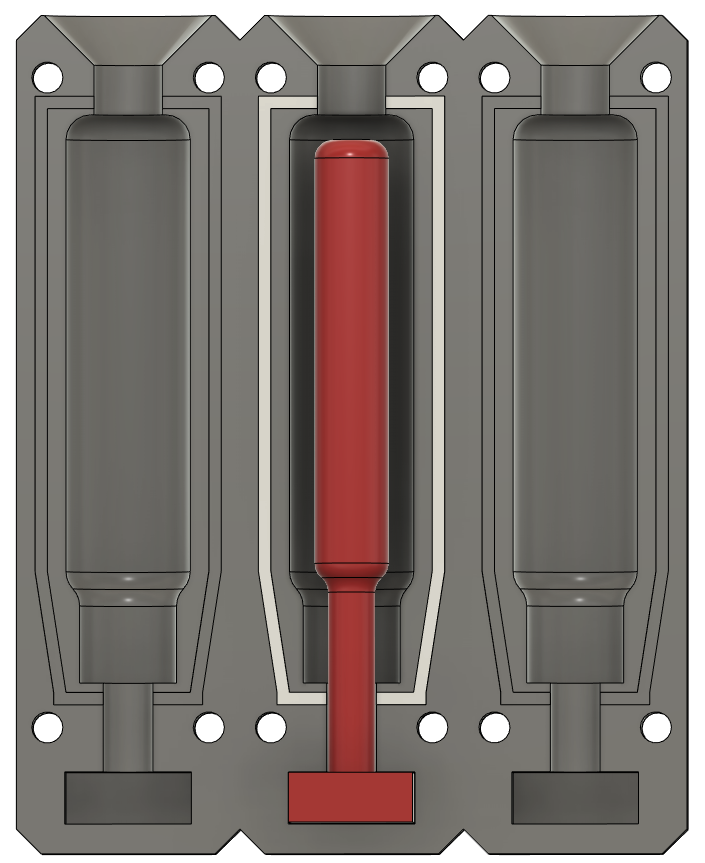
IMG/Renders/POC_5_Mold_Insert.PNG
