Mikster4/thesis/IMG/Renders/POC_5_Piston.PNG

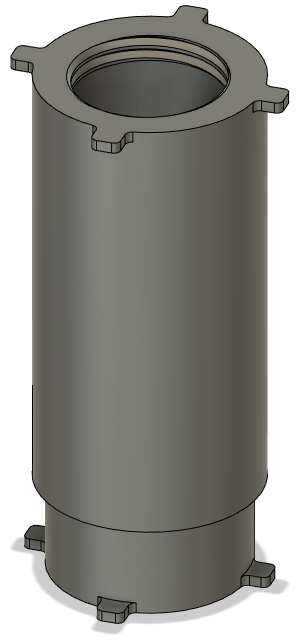
IMG/Renders/POC_5_Piston.PNG
