Mikster4/thesis/IMG/Renders/POC_5_Platform.PNG

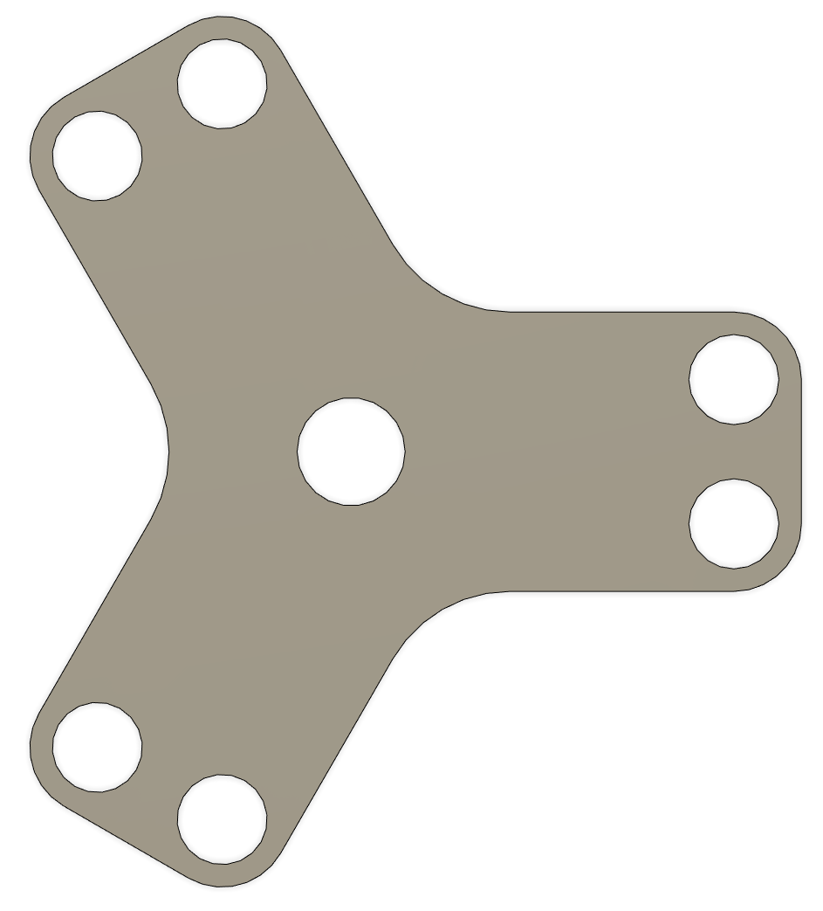
IMG/Renders/POC_5_Platform.PNG
