Mikster4/thesis/IMG/Renders/POC_5_Screw.PNG

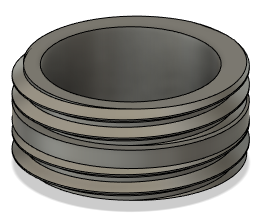
IMG/Renders/POC_5_Screw.PNG
