Mikster4/thesis/PCB/AM_Circuit_Cropped.PNG

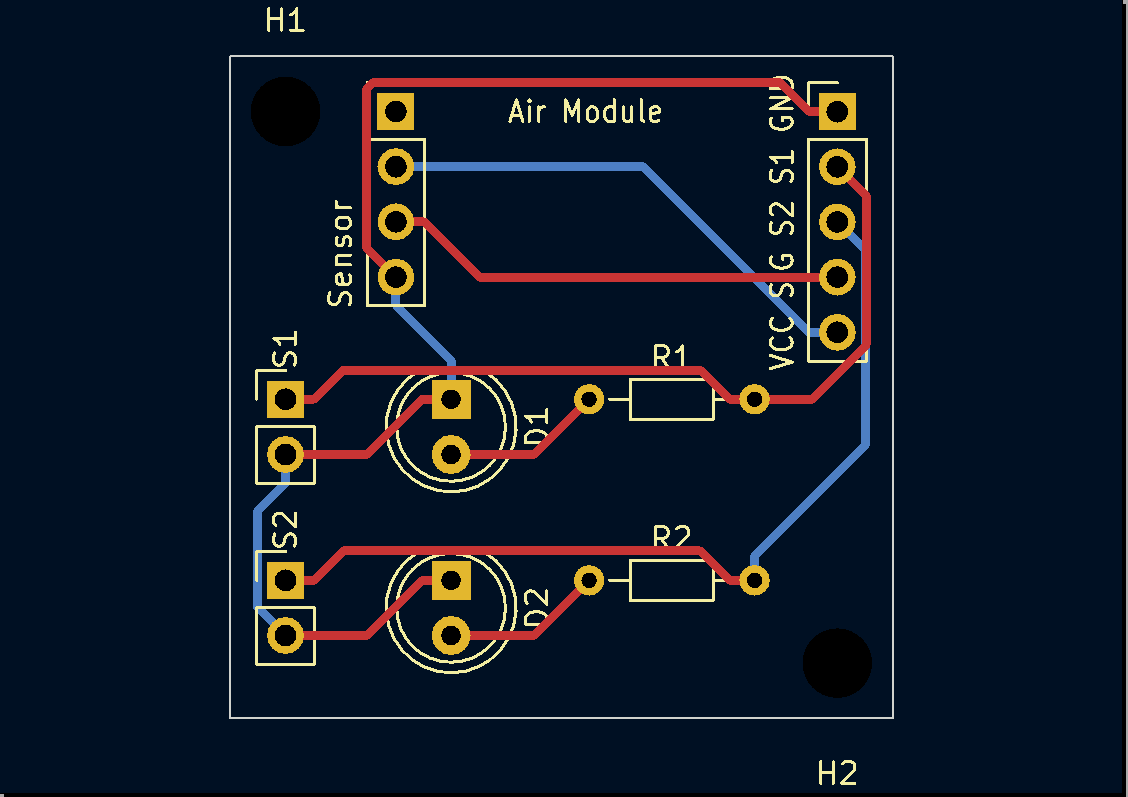
PCB/AM_Circuit_Cropped.PNG
