Mikster4/thesis/PCB/AM_Circuit_Cropped_Inv.PNG

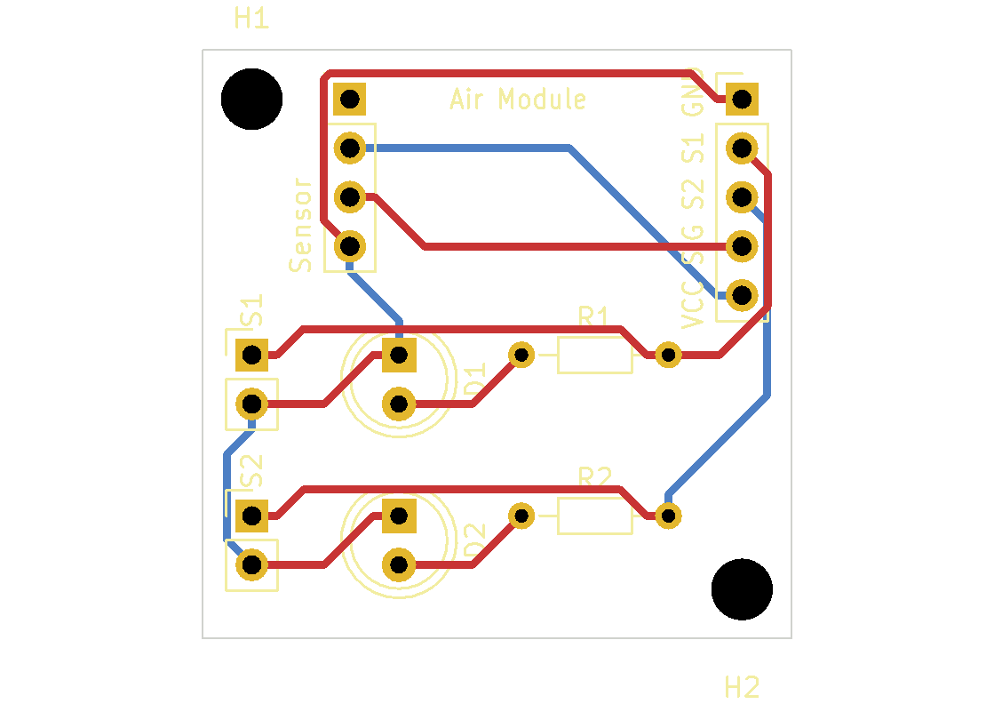
PCB/AM_Circuit_Cropped_Inv.PNG
