Mikster4/thesis/PCB/AM_Schematic_Cropped.PNG

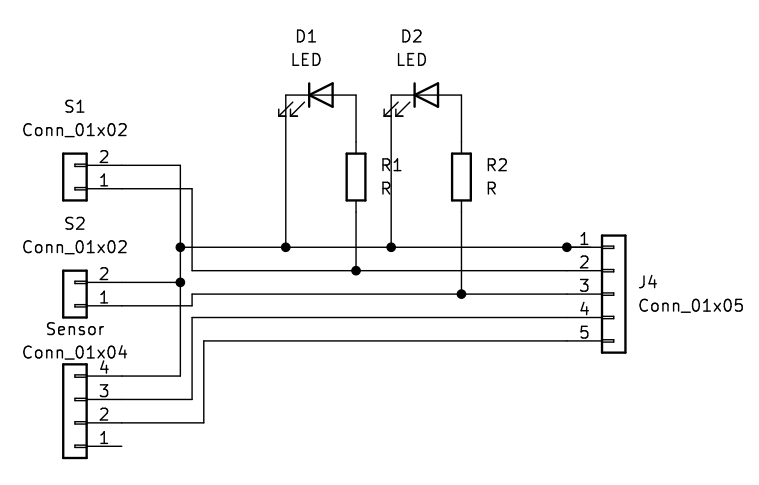
PCB/AM_Schematic_Cropped.PNG
