Mikster4/thesis/PCB/BMA_Circuit_Cropped.PNG

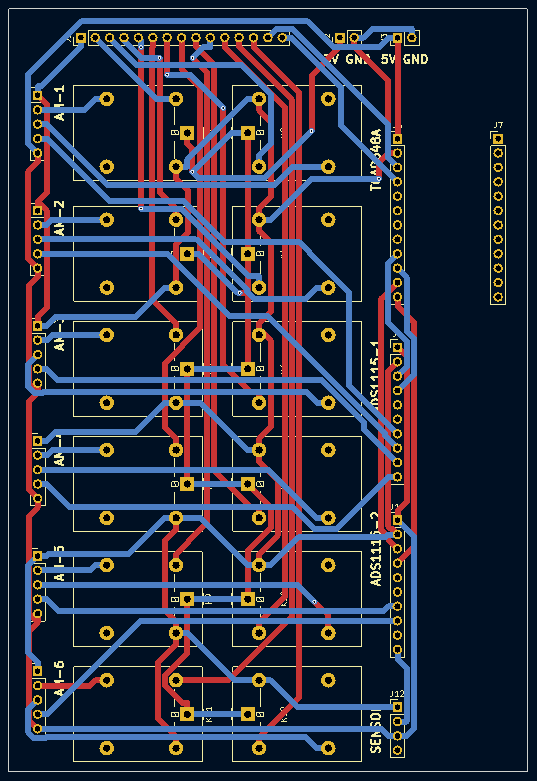
PCB/BMA_Circuit_Cropped.PNG
