Mikster4/thesis/PCB/BMA_Schematic_Cropped.PNG

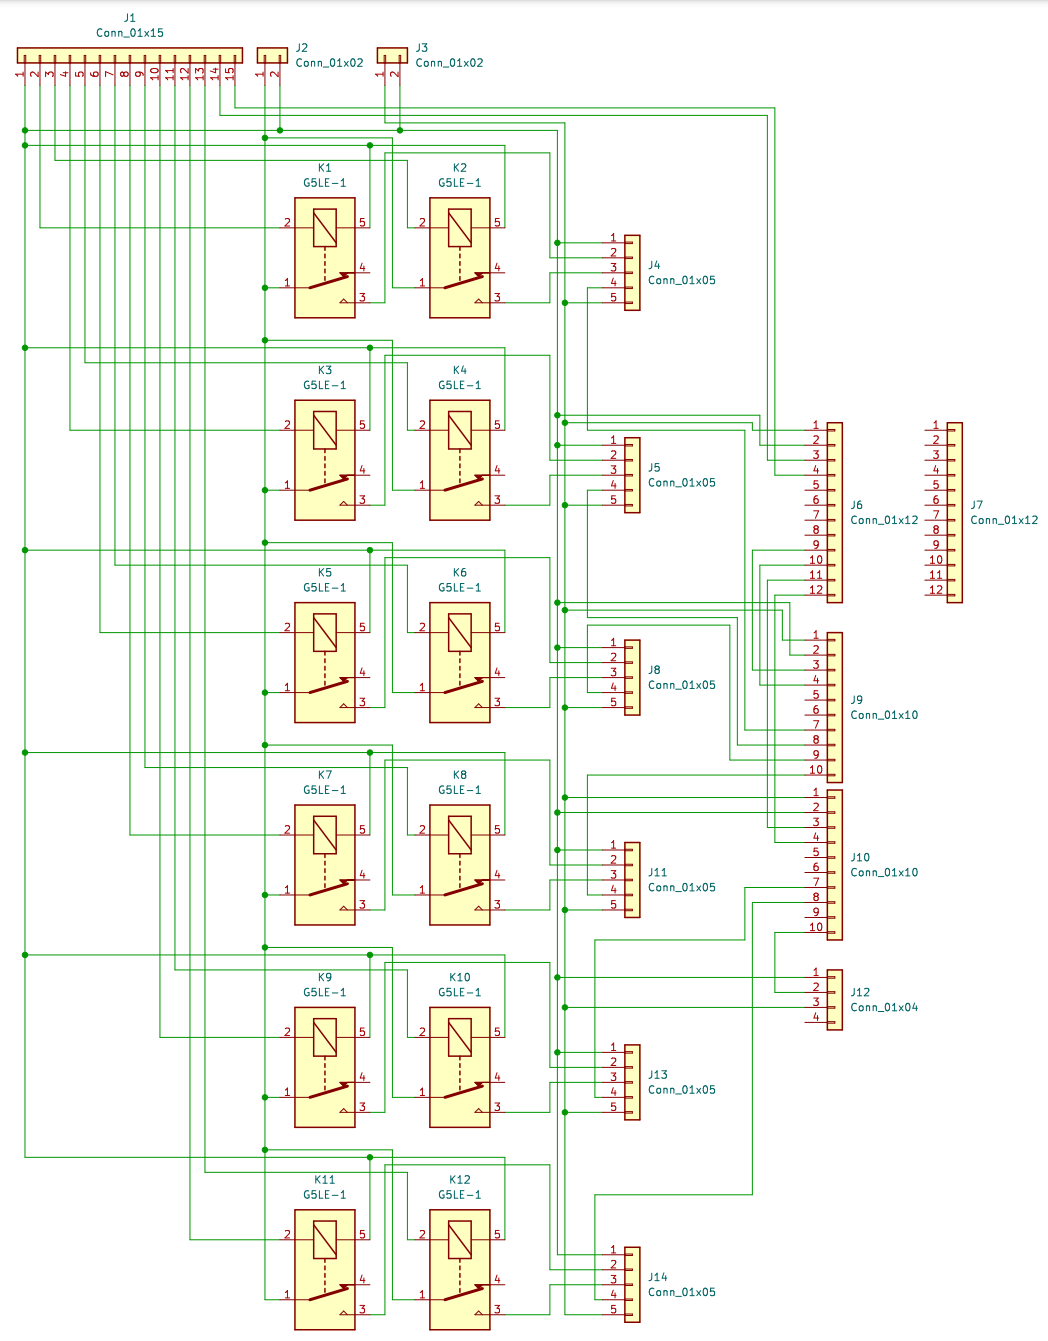
PCB/BMA_Schematic_Cropped.PNG
