Mikster4/thesis/CAD/POC 1/POC_1_Insert.stl

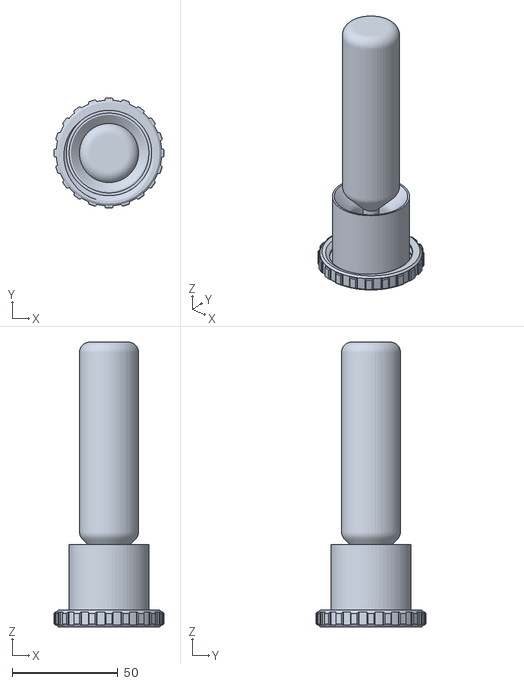
[picture p128: CAD file, 2023-01-24]
CAD/POC 1/POC_1_Insert.stl
52.0 x 52.0 x 135.0
