Mikster4/thesis/CAD/POC 5/POC_5_Insert.stl

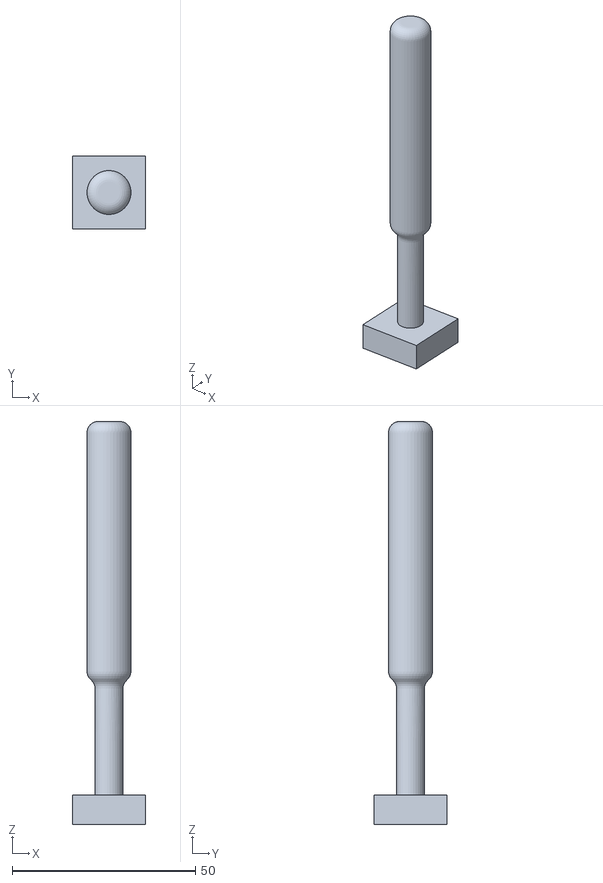
[picture p129: CAD file, 2023-01-24]
CAD/POC 5/POC_5_Insert.stl
20.0 x 20.0 x 110.0
