Mikster4/thesis/CAD/POC 2/POC_2_Base_Upper.stl

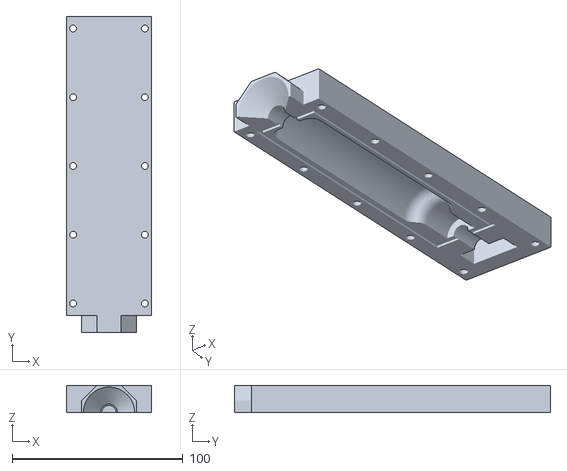
[picture p130: CAD file, 2023-01-24]
CAD/POC 2/POC_2_Base_Upper.stl
50.0 x 185.0 x 16.0
