Mikster4/thesis/CAD/POC 5/POC_5_Pistion_Outer.stl

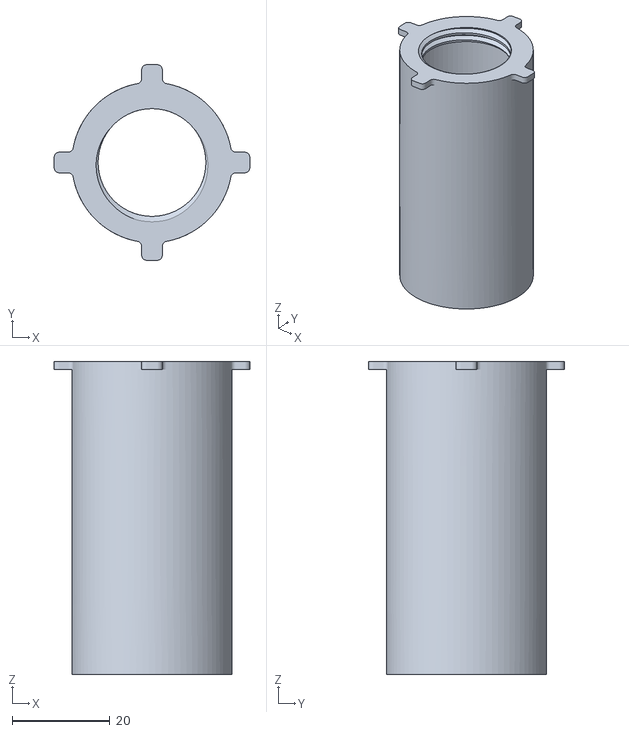
[picture p131: CAD file, 2023-01-24]
CAD/POC 5/POC_5_Pistion_Outer.stl
40.0 x 40.0 x 64.0
