Mikster4/thesis/CAD/POC 5/POC_5_Mold_Case.3mf

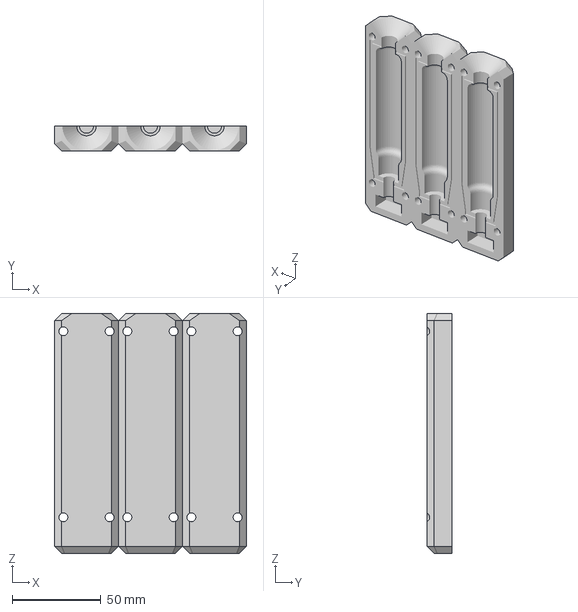
[picture p132: CAD file, 2023-01-24]
CAD/POC 5/POC_5_Mold_Case.3mf
108.0 x 14.0 x 135.0 mm
