Mikster4/thesis/CAD/POC 5/POC_5_Pistion_Inner.stl

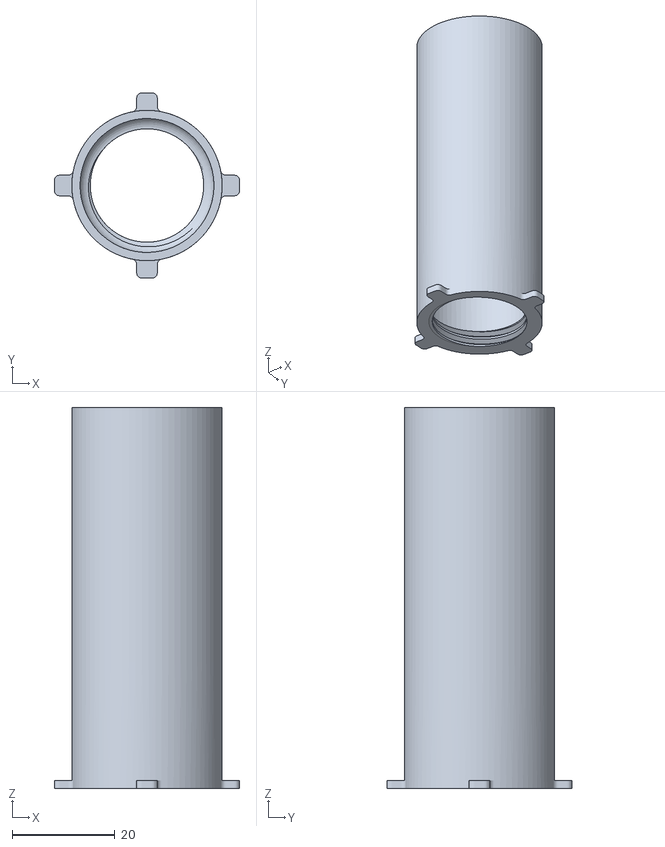
[picture p133: CAD file, 2023-01-24]
CAD/POC 5/POC_5_Pistion_Inner.stl
36.0 x 36.0 x 74.0
