Mikster4/thesis/CAD/POC 5/POC_5_Joint_Platform_Thin.stl

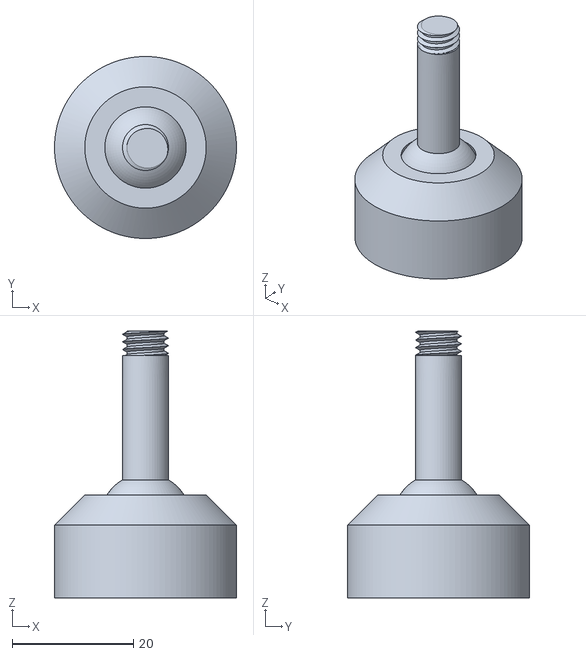
[picture p134: CAD file, 2023-01-15]
CAD/POC 5/POC_5_Joint_Platform_Thin.stl
30.0 x 30.0 x 44.0
