Mikster4/thesis/CAD/POC 5/POC_5_Oring.3mf

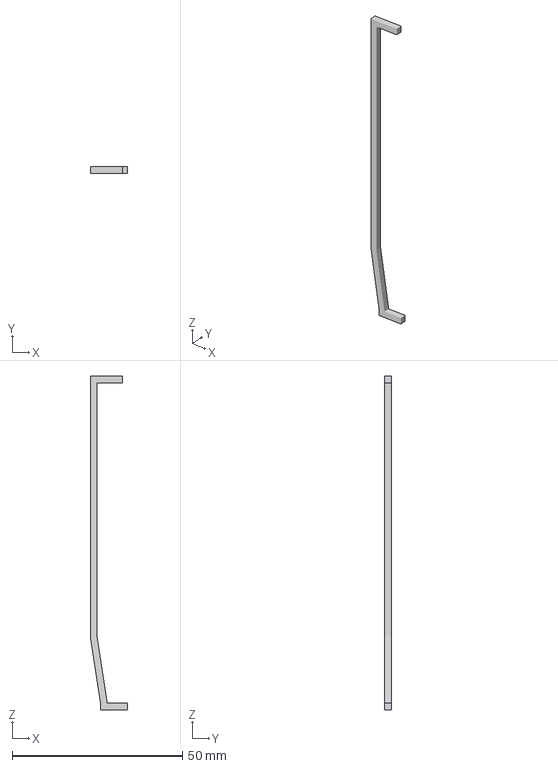
[picture p135: CAD file, 2023-01-15]
CAD/POC 5/POC_5_Oring.3mf
11.0 x 2.00 x 98.0 mm
