Mikster4/thesis/CAD/POC 5/POC_5_Joint_Base.stl.stl

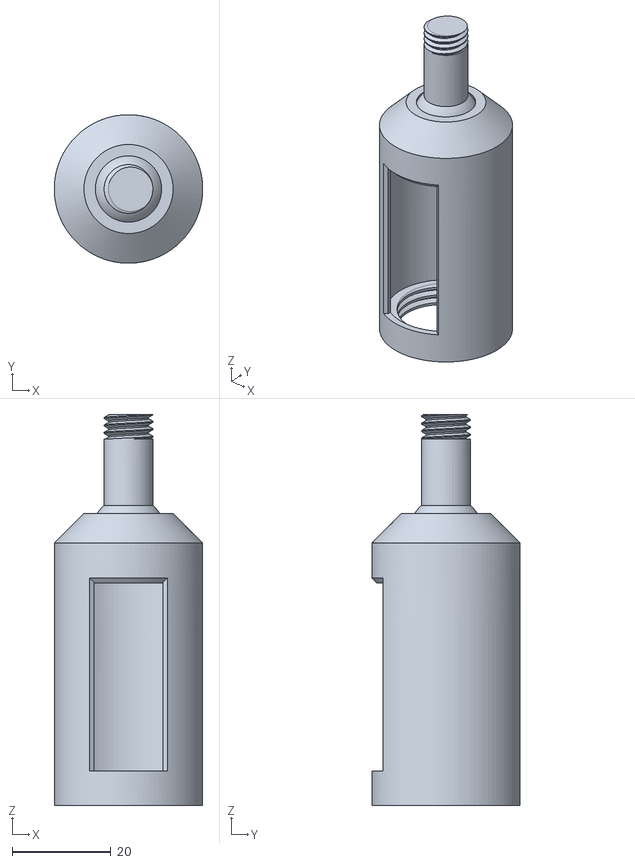
[picture p136: CAD file, 2023-01-15]
CAD/POC 5/POC_5_Joint_Base.stl.stl
30.0 x 30.0 x 79.0
