Mikster4/thesis/CAD/POC 5/POC_5_Flex_Joint.3mf

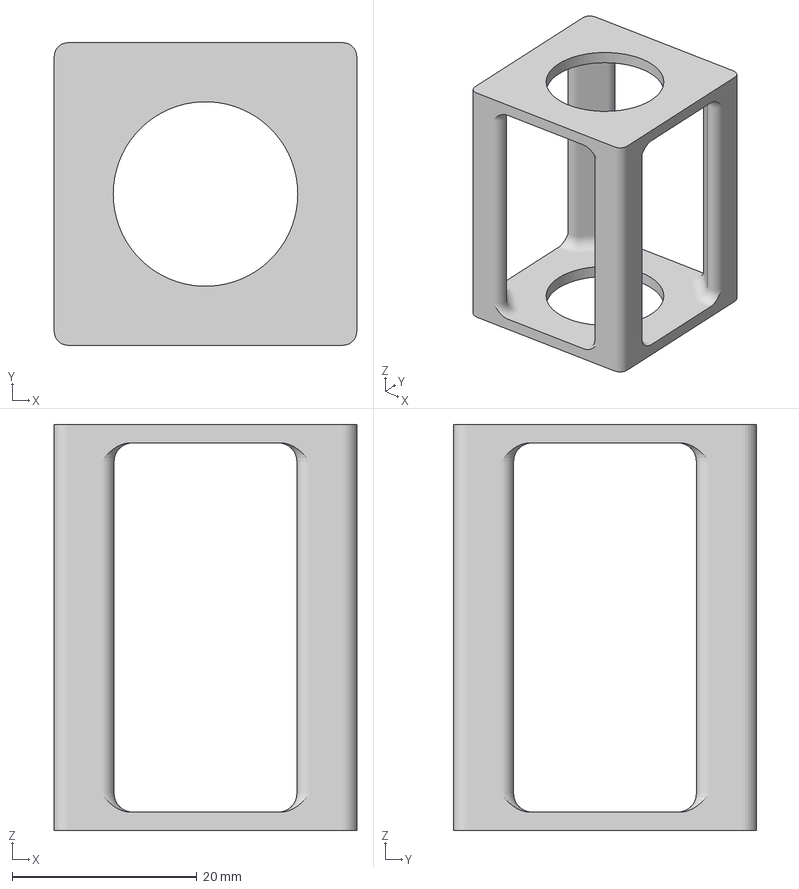
[picture p137: CAD file, 2023-01-15]
CAD/POC 5/POC_5_Flex_Joint.3mf
32.8 x 32.8 x 44.0 mm
