Mikster4/thesis/CAD/POC 5/POC_5_Joint_Platform_Reinforced.stl.stl

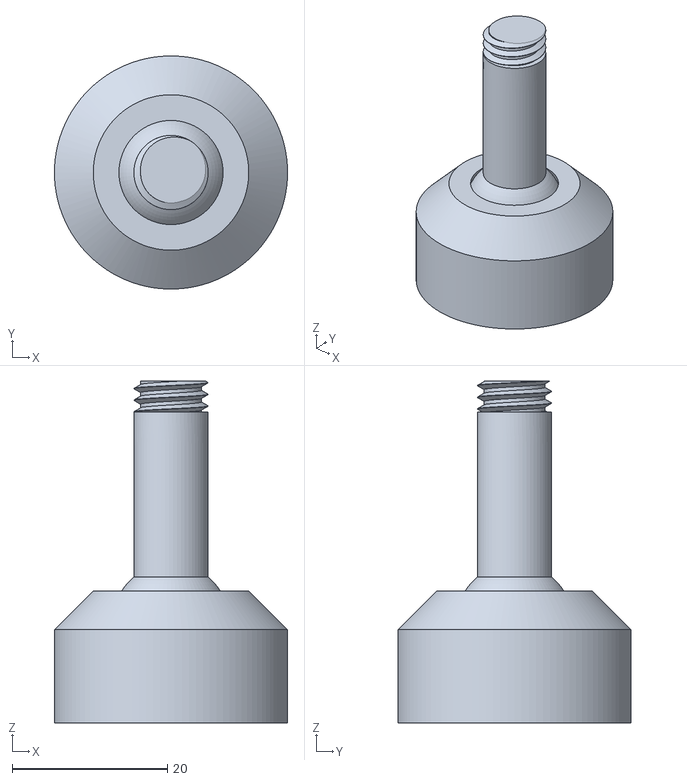
[picture p138: CAD file, 2023-01-15]
CAD/POC 5/POC_5_Joint_Platform_Reinforced.stl.stl
30.0 x 30.0 x 44.0
