Mikster4/thesis/IMG/Photos/Manufacturing/IMG_20230119_070639.jpg

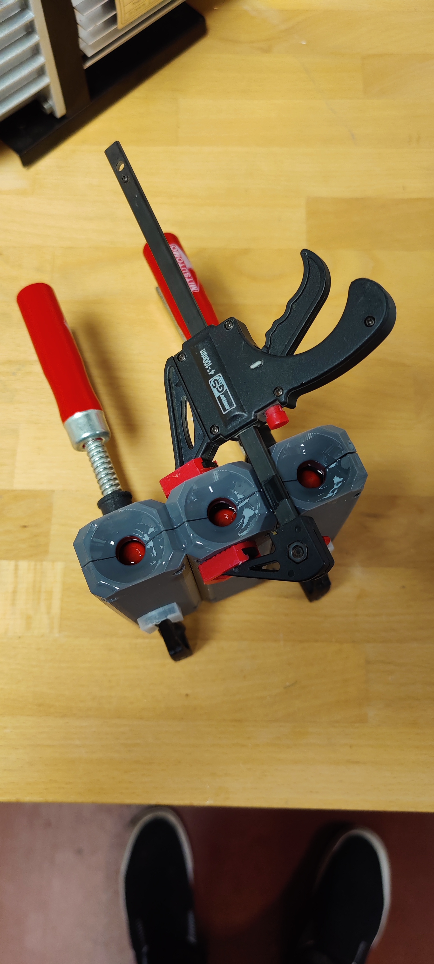
IMG/Photos/Manufacturing/IMG_20230119_070639.jpg
