Mikster4/thesis/IMG/Photos/Testing/tmp_setup.jpg

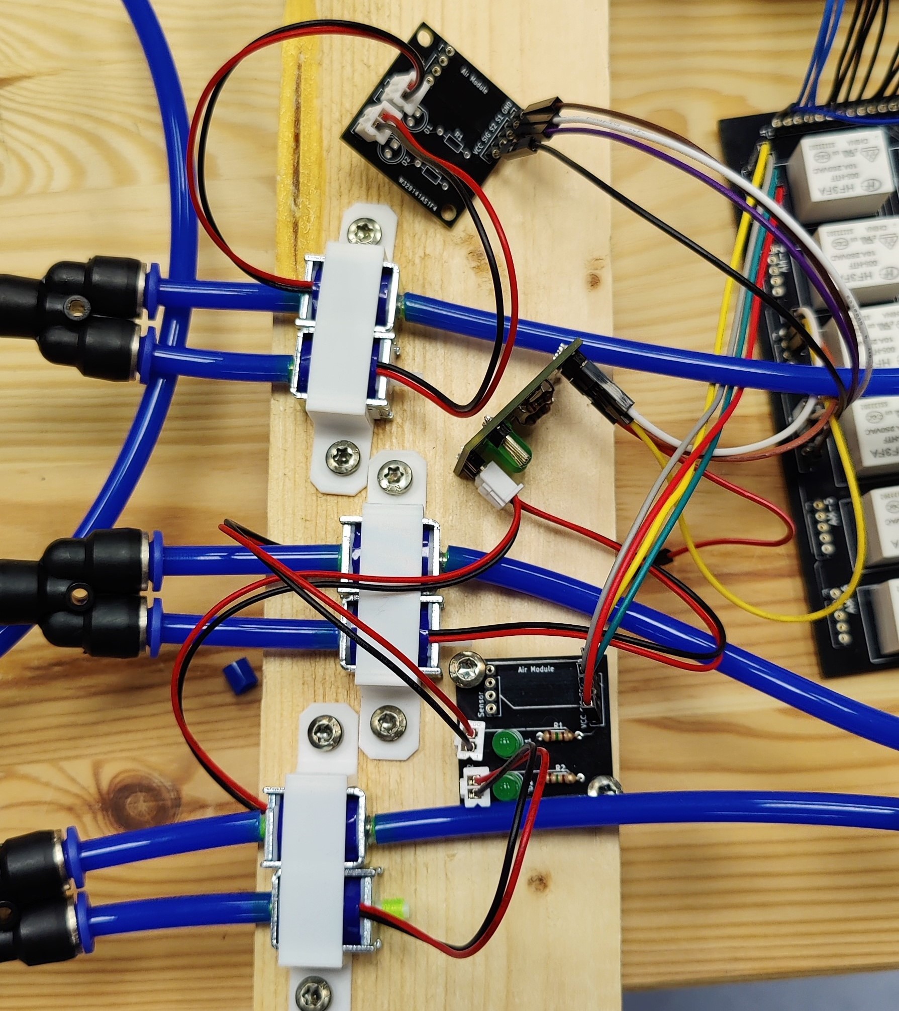
IMG/Photos/Testing/tmp_setup.jpg
