Mikster4/thesis/IMG/Photos/Testing/tmp_setup_full.jpg

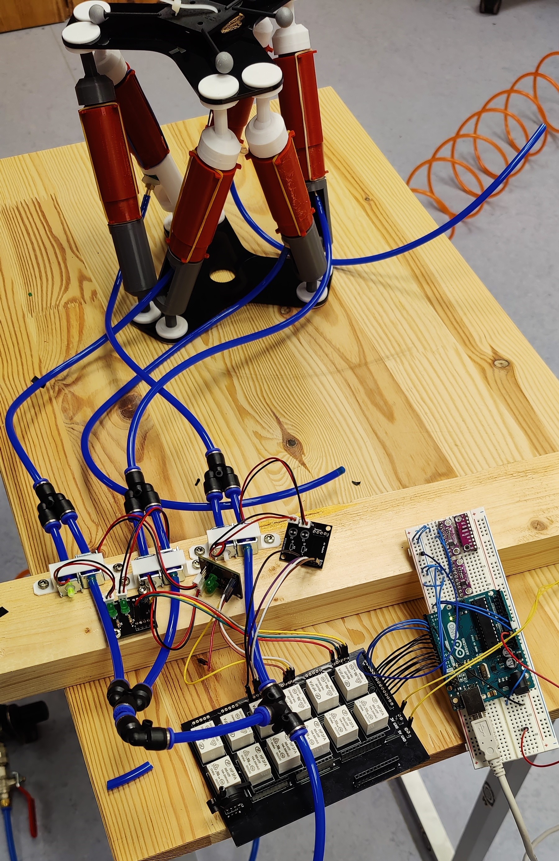
IMG/Photos/Testing/tmp_setup_full.jpg
