Mikster4/thesis/Code/data/Test_Linear.csv

Frame | Time (Seconds) | X | Y | Z | X | Y | Z
0 | 0.000000 | 177.794846 | -6.210822 | 0.444512 | -1.608008 | 215.161209 | -18.749807
1 | 0.008333 | 177.793671 | -6.209643 | 0.451396 | -1.613131 | 215.162689 | -18.752071
2 | 0.016667 | 177.786224 | -6.212403 | 0.442778 | -1.599890 | 215.166901 | -18.750473
3 | 0.025000 | 177.795975 | -6.210136 | 0.443245 | -1.588035 | 215.159225 | -18.743593
4 | 0.033333 | 177.794128 | -6.210785 | 0.445673 | -1.570543 | 215.163818 | -18.742050
5 | 0.041667 | 177.793381 | -6.213092 | 0.450952 | -1.572750 | 215.153748 | -18.738197
6 | 0.050000 | 177.798141 | -6.212439 | 0.445287 | -1.584056 | 215.158035 | -18.735449
7 | 0.058333 | 177.792862 | -6.211991 | 0.446513 | -1.589433 | 215.161011 | -18.736000
8 | 0.066667 | 177.795731 | -6.213840 | 0.452339 | -1.597104 | 215.162354 | -18.739391
9 | 0.075000 | 177.795471 | -6.211770 | 0.447800 | -1.595078 | 215.166275 | -18.741385
10 | 0.083333 | 177.794266 | -6.211539 | 0.449875 | -1.587853 | 215.163330 | -18.740377
11 | 0.091667 | 177.794434 | -6.214732 | 0.449542 | -1.585654 | 215.157349 | -18.747429
12 | 0.100000 | 177.796585 | -6.212915 | 0.443792 | -1.585851 | 215.161118 | -18.750118
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
