Mikster4/thesis/Code/data/Test_Max_Roll.csv

Frame | Time (Seconds) | X | Y | Z | X | Y | Z
0 | 0.000000 | 177.835953 | -5.883974 | -0.099834 | -3.261274 | 215.204803 | -20.608013
1 | 0.008333 | 177.851486 | -5.894504 | -0.137900 | -3.255833 | 215.241425 | -20.624025
3 | 0.025000 | 177.836441 | -5.883332 | -0.099632 | -3.259745 | 215.206924 | -20.580471
4 | 0.033333 | 177.834885 | -5.881853 | -0.095765 | -3.258579 | 215.209869 | -20.577263
5 | 0.041667 | 177.835617 | -5.882613 | -0.092521 | -3.266319 | 215.201065 | -20.577524
6 | 0.050000 | 177.831161 | -5.884920 | -0.097622 | -3.278350 | 215.204254 | -20.584467
7 | 0.058333 | 177.836960 | -5.884390 | -0.095304 | -3.286112 | 215.199081 | -20.594683
8 | 0.066667 | 177.832535 | -5.883125 | -0.097606 | -3.285113 | 215.203781 | -20.605370
9 | 0.075000 | 177.835678 | -5.882232 | -0.092445 | -3.268307 | 215.204147 | -20.612246
10 | 0.083333 | 177.837219 | -5.881203 | -0.094544 | -3.253882 | 215.203735 | -20.605261
11 | 0.091667 | 177.841873 | -5.881623 | -0.083839 | -3.252422 | 215.199707 | -20.597898
12 | 0.100000 | 177.838272 | -5.882352 | -0.091089 | -3.260606 | 215.206253 | -20.590254
13 | 0.108333 | 177.834259 | -5.883028 | -0.093264 | -3.270560 | 215.204376 | -20.586052
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
