Mikster4/thesis/Code/data/Test_Max_Yaw.csv

Frame | Time (Seconds) | X | Y | Z | X | Y | Z
0 | 0.000000 | 174.614151 | -43.459545 | -4.486455 | -20.243649 | 219.046600 | -52.946980
1 | 0.008333 | 174.626541 | -43.460739 | -4.500926 | -20.241215 | 219.047058 | -52.947483
2 | 0.016667 | 174.625870 | -43.460491 | -4.493520 | -20.249966 | 219.034973 | -52.948891
3 | 0.025000 | 174.620407 | -43.460667 | -4.497962 | -20.255085 | 219.043152 | -52.948868
4 | 0.033333 | 174.639648 | -43.457287 | -4.498140 | -20.252600 | 219.047272 | -52.951077
5 | 0.041667 | 174.619736 | -43.460667 | -4.498451 | -20.250231 | 219.041031 | -52.955074
6 | 0.050000 | 174.619064 | -43.459152 | -4.469200 | -20.253428 | 219.011749 | -52.943260
7 | 0.058333 | 174.631393 | -43.459808 | -4.497834 | -20.245085 | 219.039780 | -52.956814
8 | 0.066667 | 174.626129 | -43.461071 | -4.490601 | -20.242786 | 219.037201 | -52.959419
9 | 0.075000 | 174.621841 | -43.462818 | -4.484450 | -20.247101 | 219.035324 | -52.955322
10 | 0.083333 | 174.629990 | -43.458626 | -4.496184 | -20.247976 | 219.053284 | -52.947502
11 | 0.091667 | 174.626099 | -43.460339 | -4.493136 | -20.251446 | 219.032364 | -52.952038
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
