Mikster4/thesis/CODE/data/Platform_Test_0.png

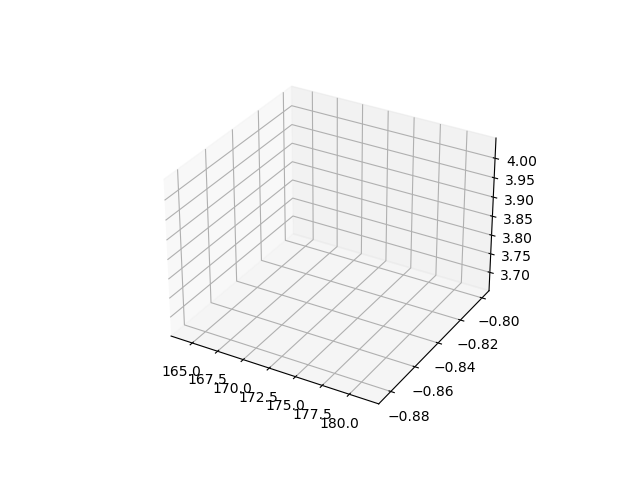
CODE/data/Platform_Test_0.png
