Mikster4/thesis/IMG/Photos/Testing/bmafin.jpg

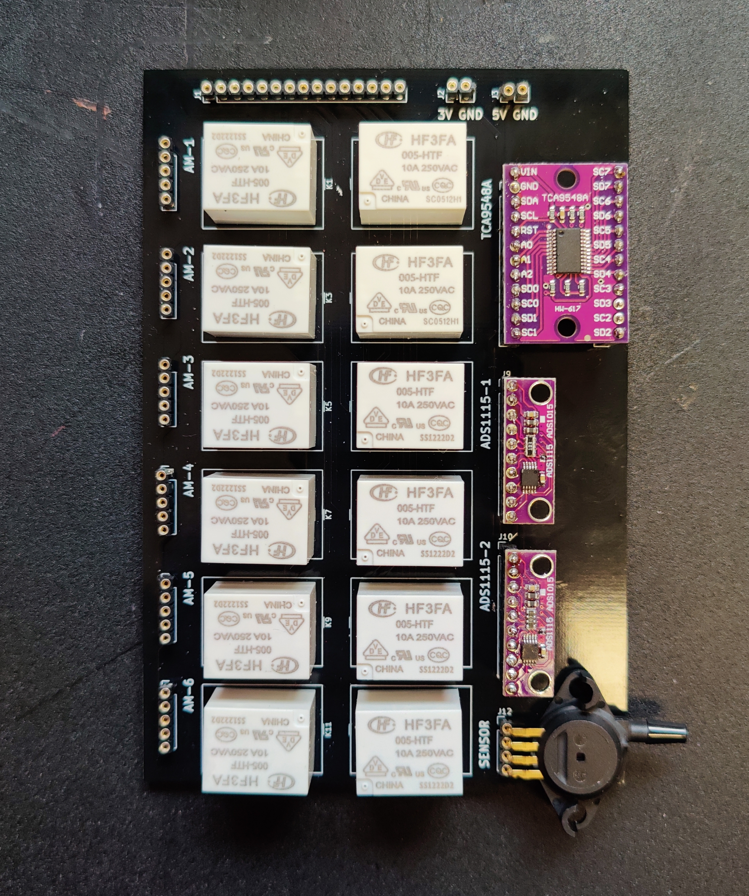
IMG/Photos/Testing/bmafin.jpg
