Mikster4/thesis/IMG/Photos/Testing/front.jpg

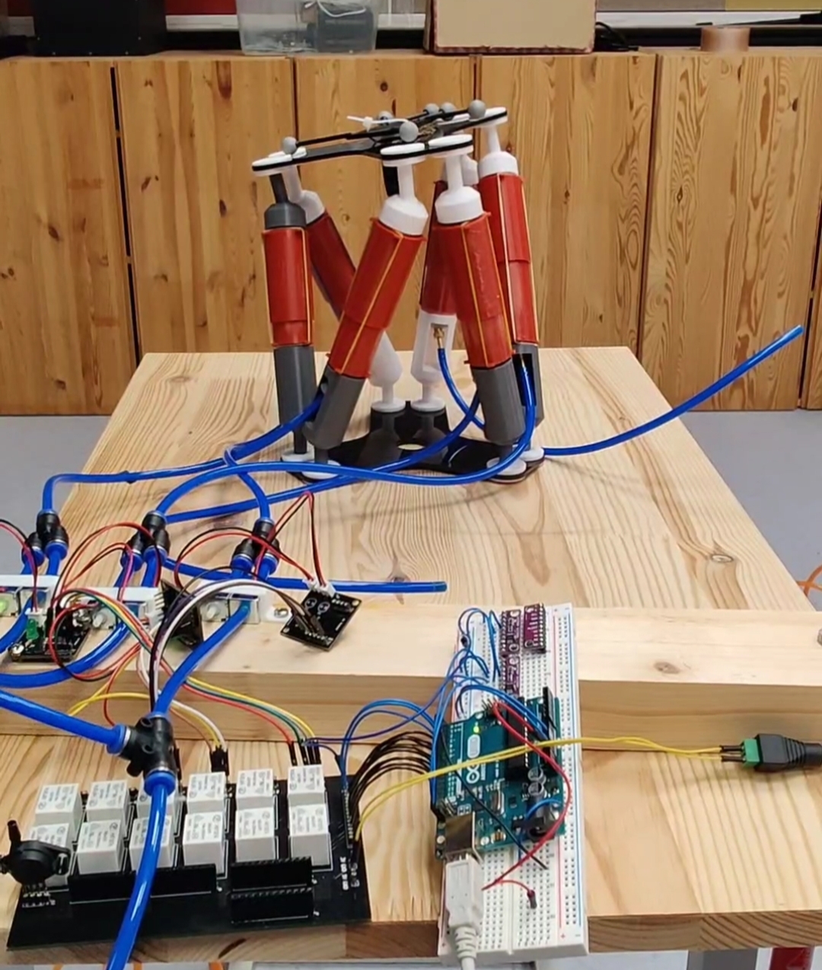
IMG/Photos/Testing/front.jpg
