Mikster4/thesis/IMG/Photos/Testing/IMG_20230308_220346.jpg

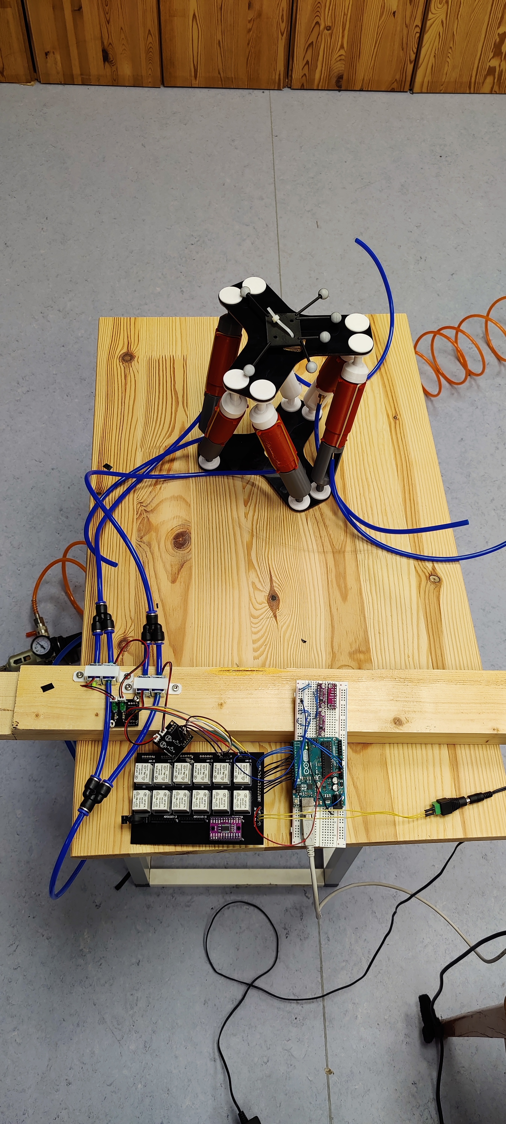
IMG/Photos/Testing/IMG_20230308_220346.jpg
