Mikster4/thesis/IMG/Photos/Testing/IMG_20230308_220409.jpg

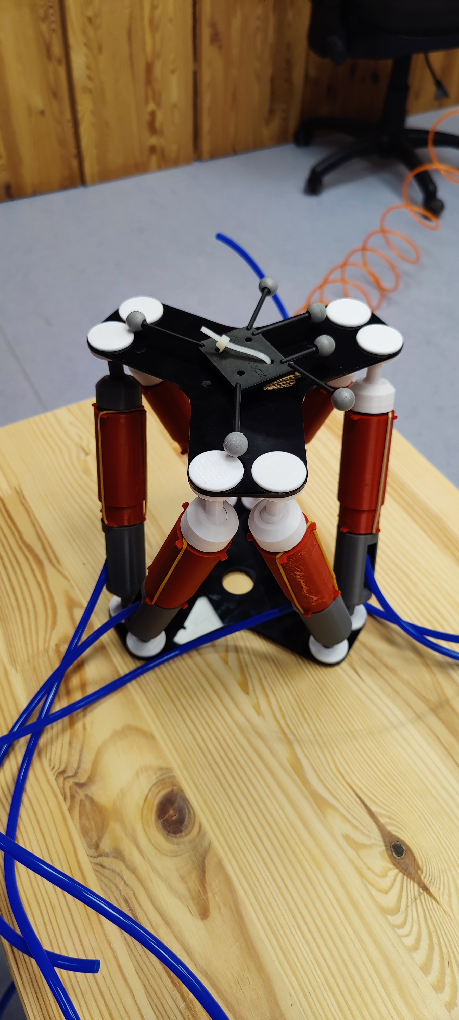
IMG/Photos/Testing/IMG_20230308_220409.jpg
