Mikster4/thesis/IMG/Photos/Testing/IMG_20230308_231445.jpg

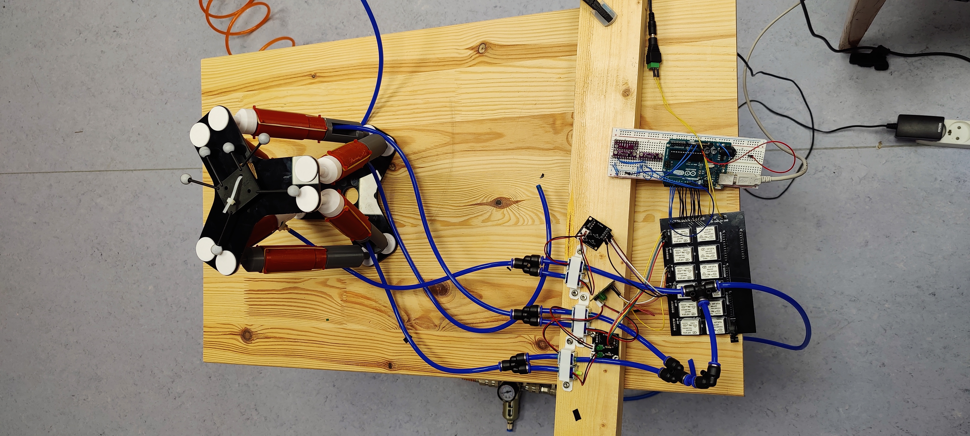
IMG/Photos/Testing/IMG_20230308_231445.jpg
