Mikster4/thesis/IMG/Photos/Testing/IMG_20230308_231456.jpg

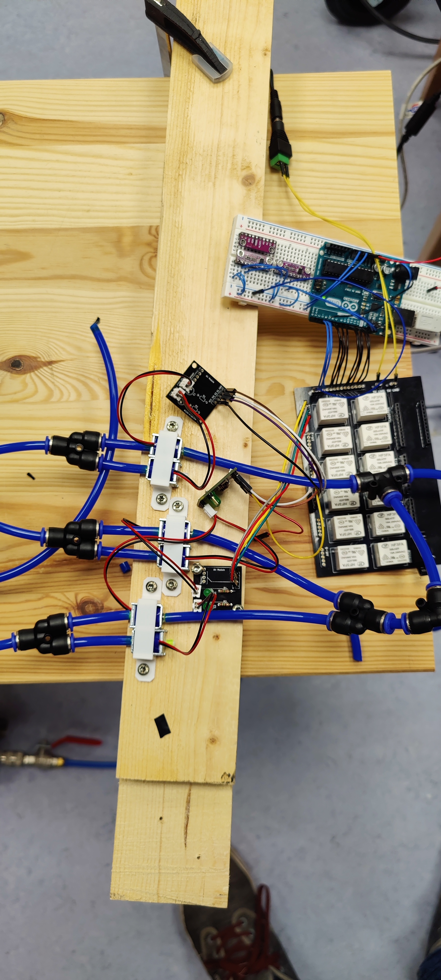
IMG/Photos/Testing/IMG_20230308_231456.jpg
