Mikster4/thesis/IMG/Photos/Testing/max_roll.jpg

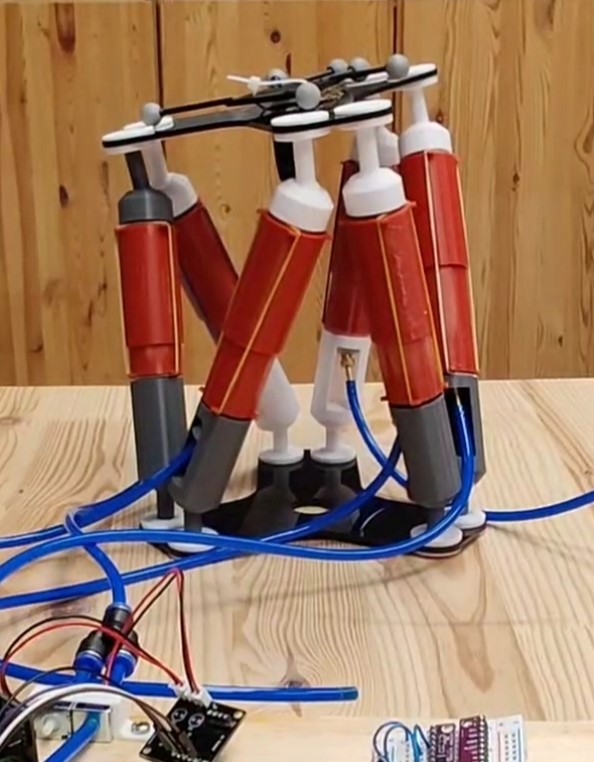
IMG/Photos/Testing/max_roll.jpg
