Mikster4/thesis/IMG/Photos/Testing/optitrack.jpg

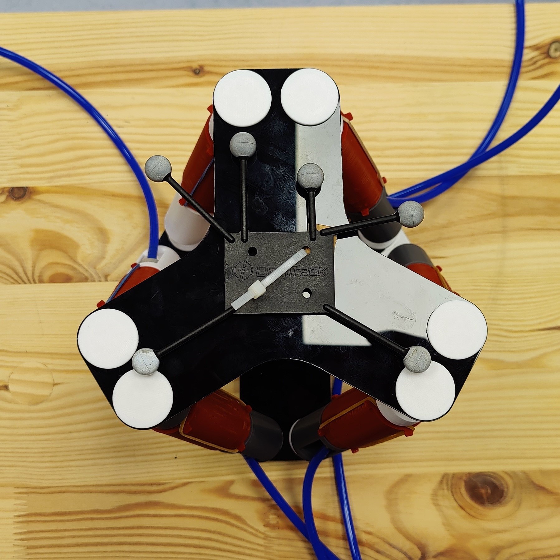
IMG/Photos/Testing/optitrack.jpg
