Mikster4/thesis/IMG/Photos/Testing/platform_close.jpg

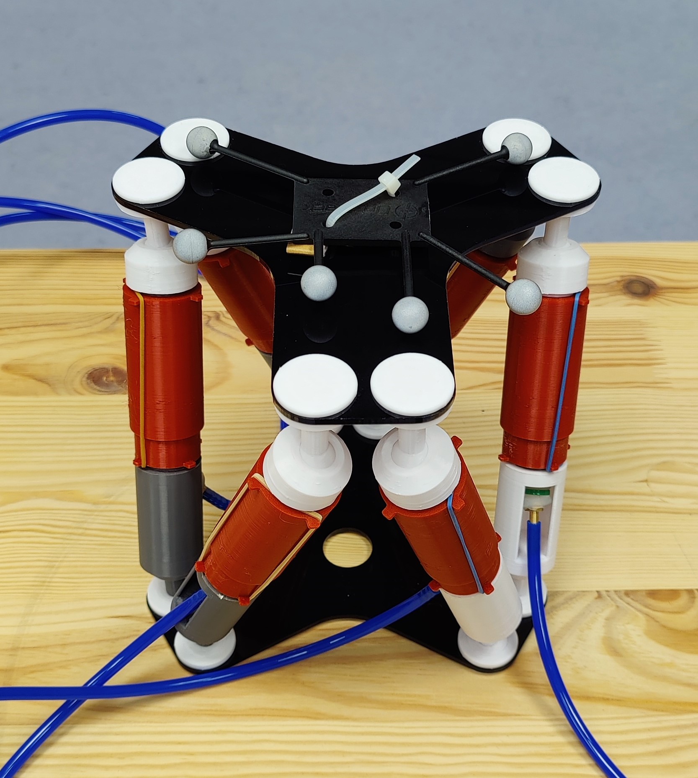
IMG/Photos/Testing/platform_close.jpg
