Mikster4/thesis/IMG/Photos/Testing/Screenshot_2023-03-09-11-24-11-10_92460851df6f172a4592fca41cc2d2e6.jpg

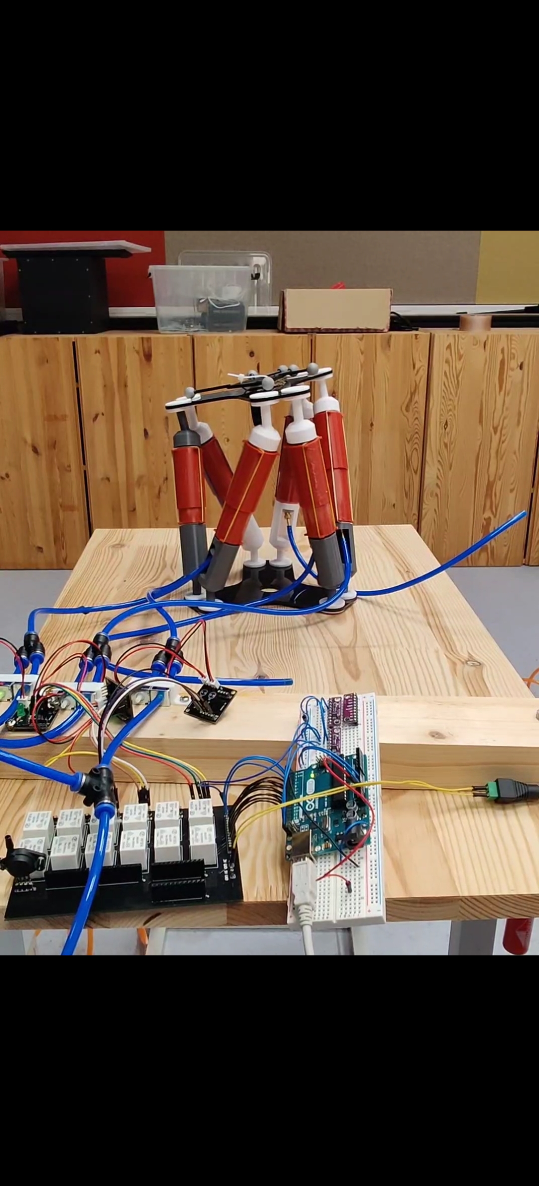
IMG/Photos/Testing/Screenshot_2023-03-09-11-24-11-10_92460851df6f172a4592fca41cc2d2e6.jpg
