Mikster4/thesis/IMG/Photos/Cores/mesh_fix_1.jpg

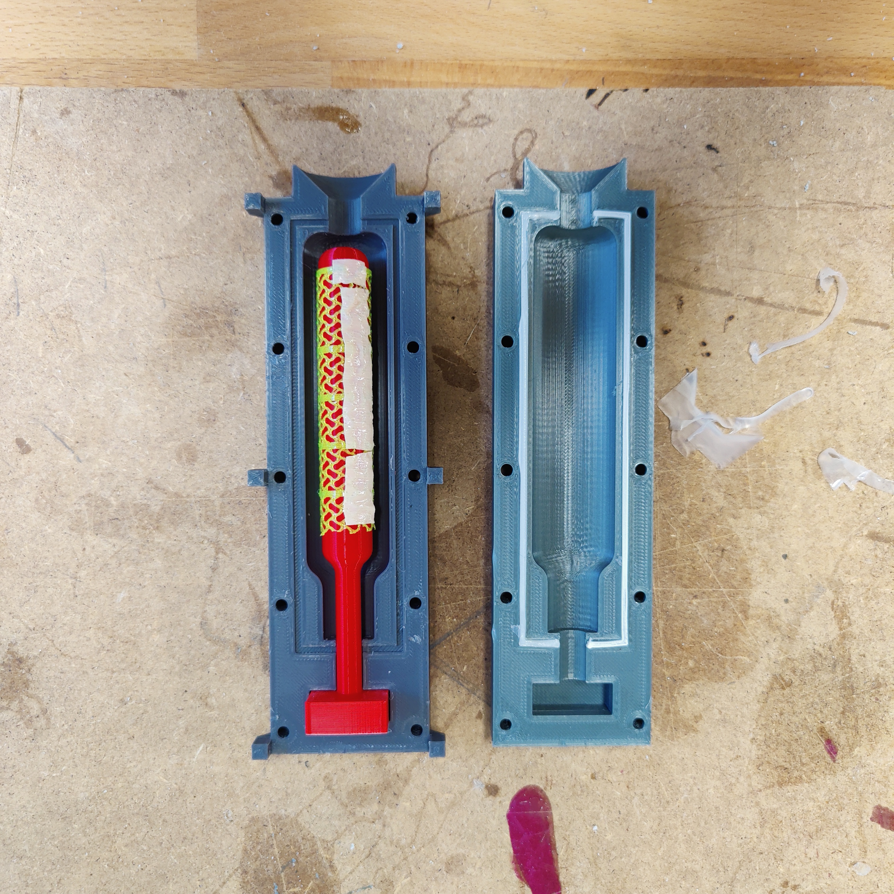
IMG/Photos/Cores/mesh_fix_1.jpg
